OpenRobotics-official/Eurobot-competition/Electronics/Carte Coupe de France/Carte temp/Carte Stepper.PNG

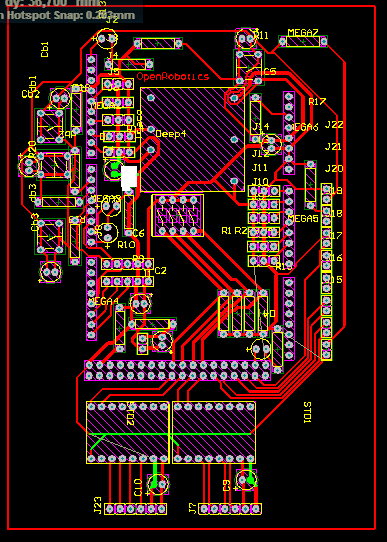
Electronics/Carte Coupe de France/Carte temp/Carte Stepper.PNG
