OpenRobotics-official/Eurobot-competition/Electronics/Carte Coupe de France/Carte temp/schematic carte stepper part1.PNG

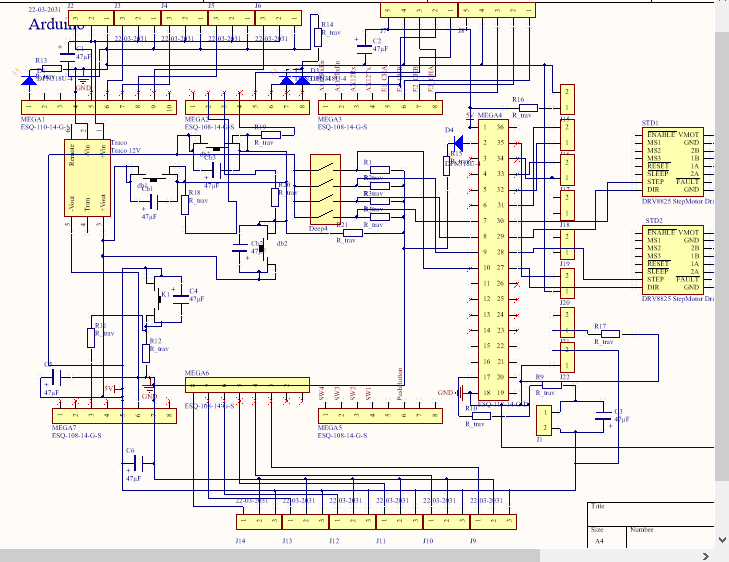
Electronics/Carte Coupe de France/Carte temp/schematic carte stepper part1.PNG
