OpenRobotics-official/Eurobot-competition/Electronics/Carte Coupe de France/Carte temp/schematic carte stepper part2.PNG

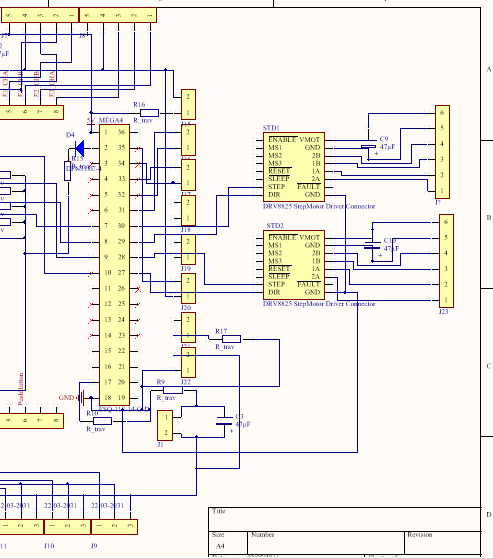
Electronics/Carte Coupe de France/Carte temp/schematic carte stepper part2.PNG
