OpenRobotics-official/Eurobot-competition/Electronics/Microcontrôleur/Screenshot_2015-12-03-18-33-24.png

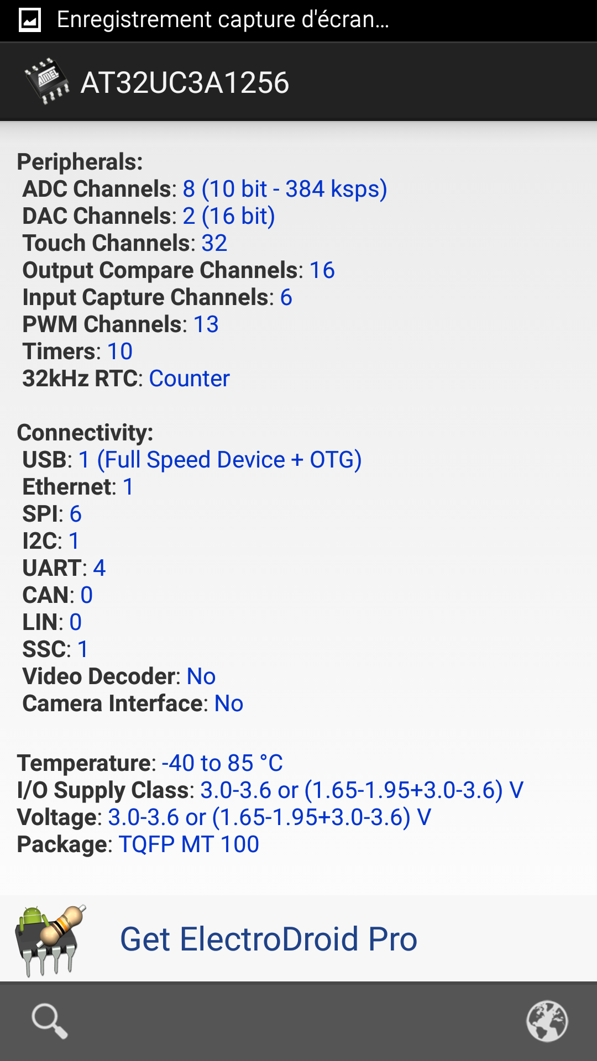
Electronics/Microcontrôleur/Screenshot_2015-12-03-18-33-24.png
