OpenRobotics-official/Eurobot-competition/wheelbase/Photo/wheelbase_trans.PNG

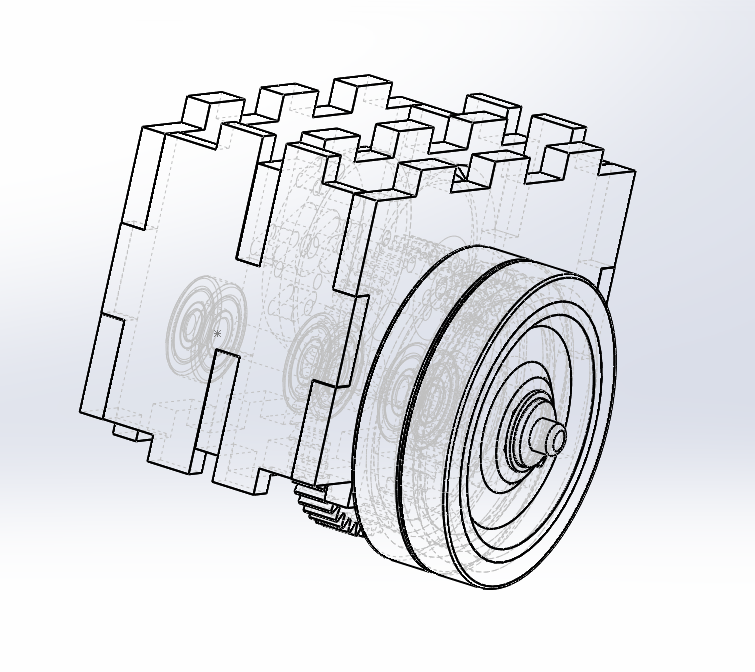
wheelbase/Photo/wheelbase_trans.PNG
