OpenRobotics-official/Eurobot-competition/wheelbase/solidworks/Base roulante lucas/base-roulante.PNG

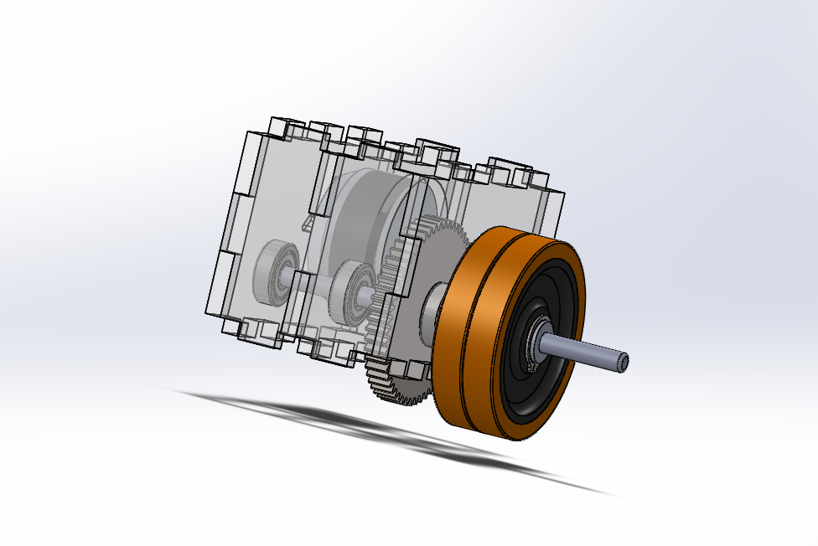
wheelbase/solidworks/Base roulante lucas/base-roulante.PNG
