OpenRobotics-official/Eurobot-competition/wheelbase/solidworks/Base roulante lucas/Banebots_double_T40.SLDASM

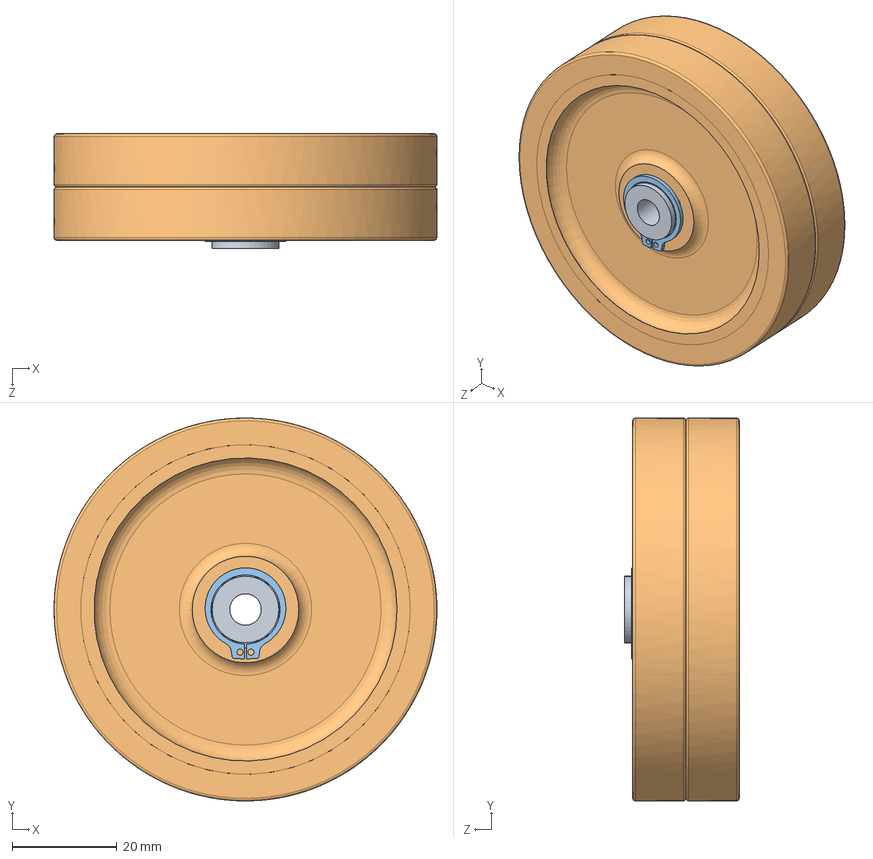
[picture p30: CAD file, 2016-05-19]
wheelbase/solidworks/Base roulante lucas/Banebots_double_T40.SLDASM
73.0 x 73.0 x 21.8 mm
T40H-SM62
BaneBots_T40 x 2
basic external retaining ring_ai
