OpenRobotics-official/Eurobot-competition/wheelbase/solidworks/Banebots_double_T40.SLDASM

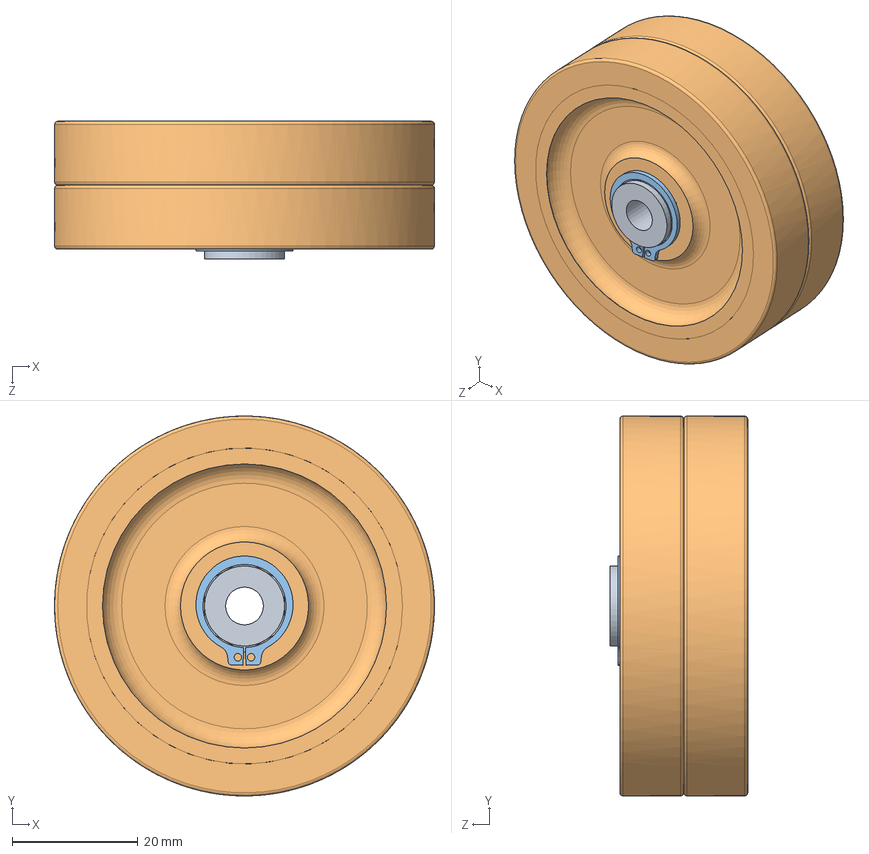
[picture p31: CAD file, 2016-05-19]
wheelbase/solidworks/Banebots_double_T40.SLDASM
60.3 x 60.3 x 21.8 mm
T40H-SM62
BaneBots_T40 x 2
basic external retaining ring_ai
