OpenRobotics-official/Eurobot-competition/3D-others/Support_axe_encondeurs.SLDPRT

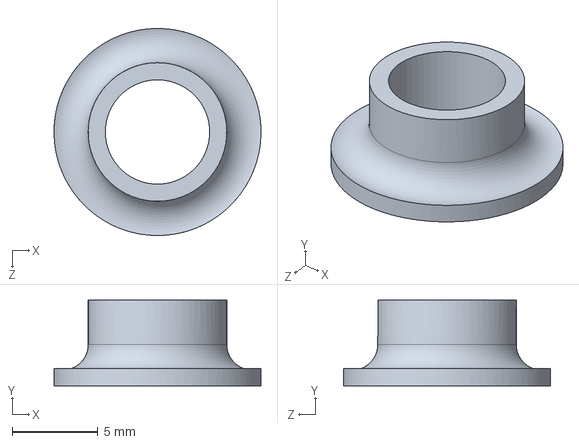
[picture p32: CAD file, 2016-05-19]
3D-others/Support_axe_encondeurs.SLDPRT
12.1 x 5.00 x 12.1 mm
