OpenRobotics-official/Eurobot-competition/Fishing arm/Support_bras_bloc.SLDPRT

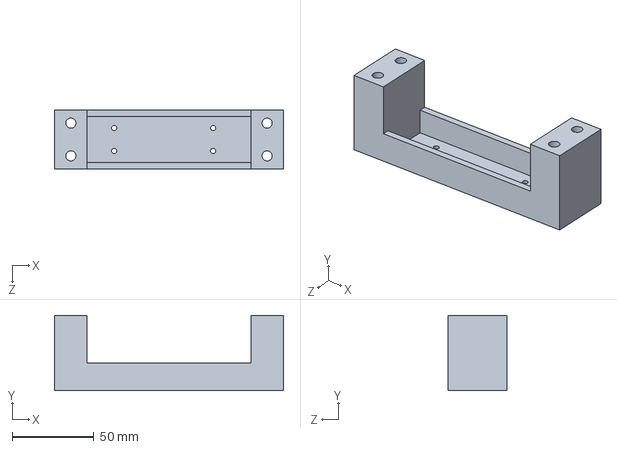
[picture p33: CAD file, 2016-05-19]
Fishing arm/Support_bras_bloc.SLDPRT
140.0 x 46.0 x 36.0 mm
