OpenRobotics-official/Eurobot-competition/Funny action/Parasol_v2/Servo.SLDPRT

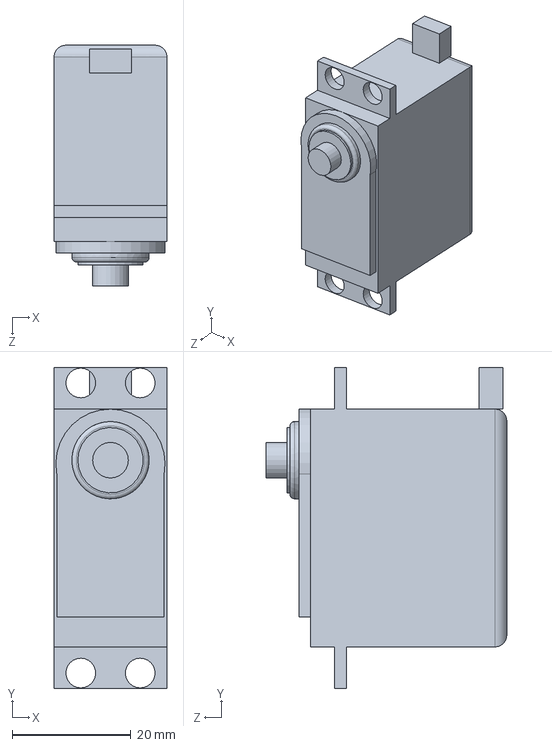
[picture p34: CAD file, 2016-05-19]
Funny action/Parasol_v2/Servo.SLDPRT
19.0 x 54.0 x 40.5 mm
