OpenRobotics-official/Eurobot-competition/wheelbase/base_dessous_V2_.DXF

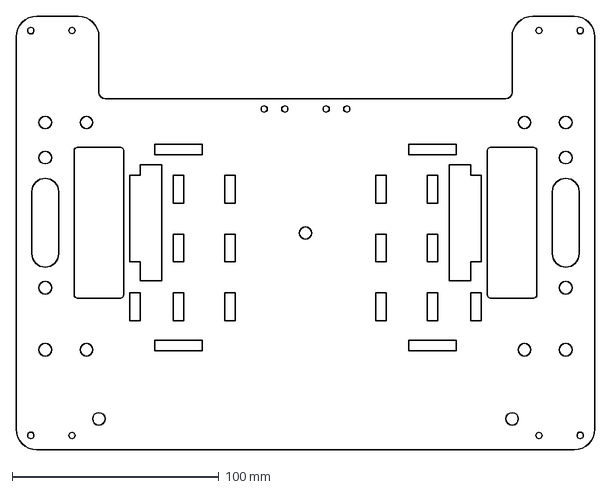
[picture p35: CAD file, 2016-05-19]
wheelbase/base_dessous_V2_.DXF
280.0 x 210.0 mm
