OpenRobotics-official/Eurobot-competition/wheelbase/Decoupe Laser/cote_long_roue.DXF

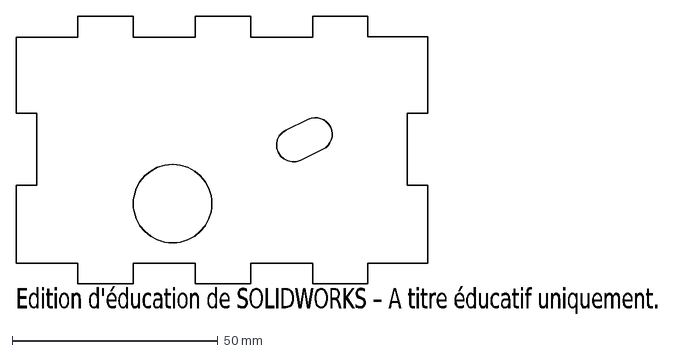
[picture p36: CAD file, 2016-05-19]
wheelbase/Decoupe Laser/cote_long_roue.DXF
Edition d'éducation de SOLIDWORKS – A titre éducatif uniquement.
