OpenRobotics-official/Eurobot-competition/wheelbase/Pieces a decouper/cote-court_50.DXF

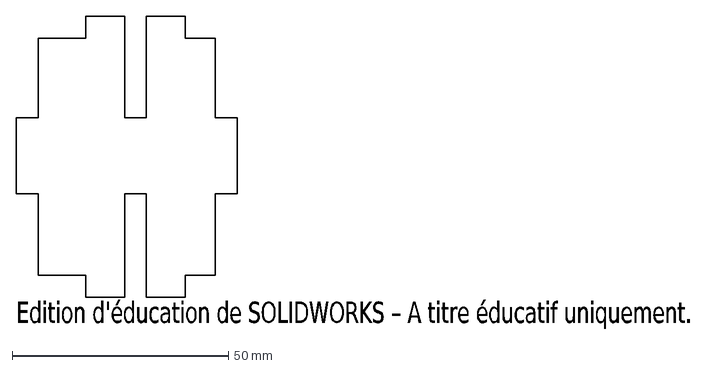
[picture p37: CAD file, 2016-05-19]
wheelbase/Pieces a decouper/cote-court_50.DXF
Edition d'éducation de SOLIDWORKS – A titre éducatif uniquement.
