OpenRobotics-official/Eurobot-competition/wheelbase/solidworks/Base roulante lucas/T40H-SM62.SLDPRT

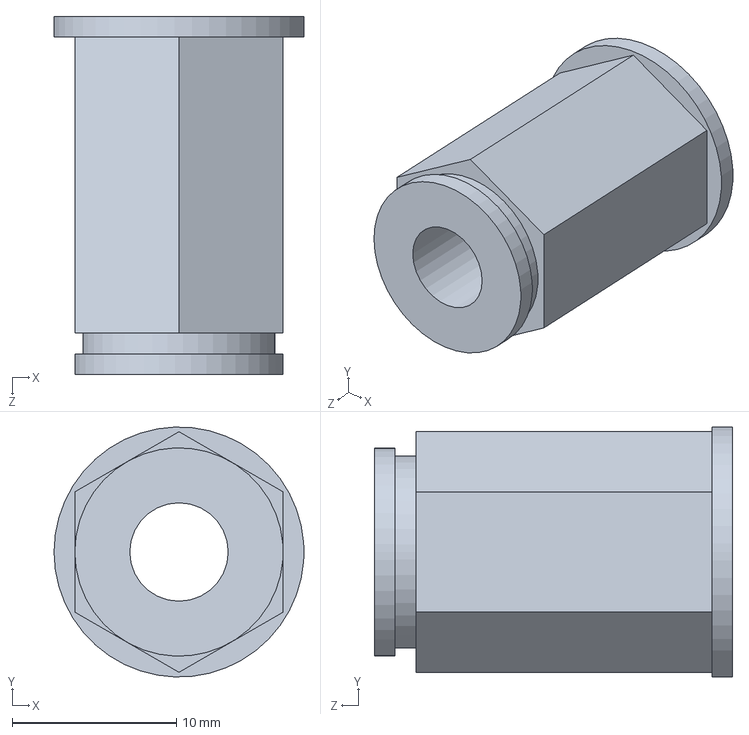
[picture p38: CAD file, 2016-05-19]
wheelbase/solidworks/Base roulante lucas/T40H-SM62.SLDPRT
15.2 x 15.2 x 21.8 mm
