OpenRobotics-official/Eurobot-competition/wheelbase/solidworks/STL/base_finale_style.STL

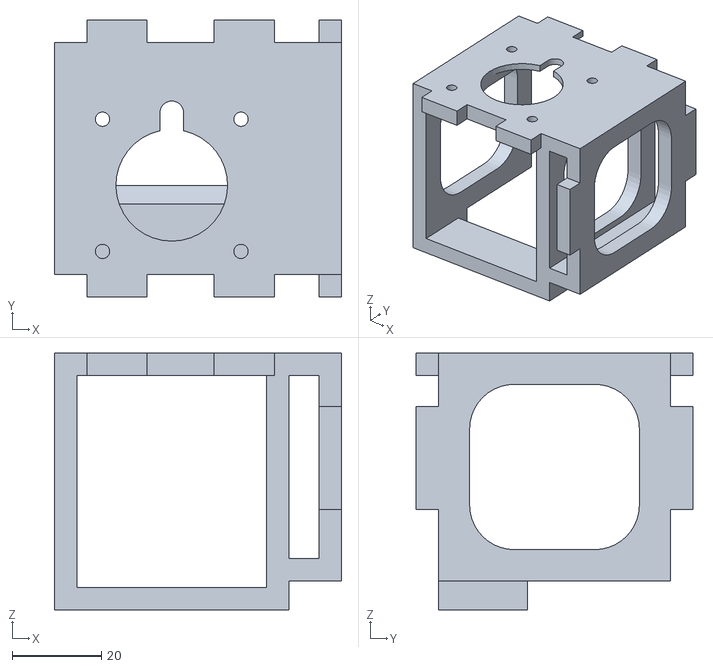
[picture p39: CAD file, 2016-05-19]
wheelbase/solidworks/STL/base_finale_style.STL
64.2 x 62.0 x 57.5
