OpenRobotics-official/Eurobot-competition/wheelbase/solidworks/U_jante_roue_POSIC_v4.SLDPRT

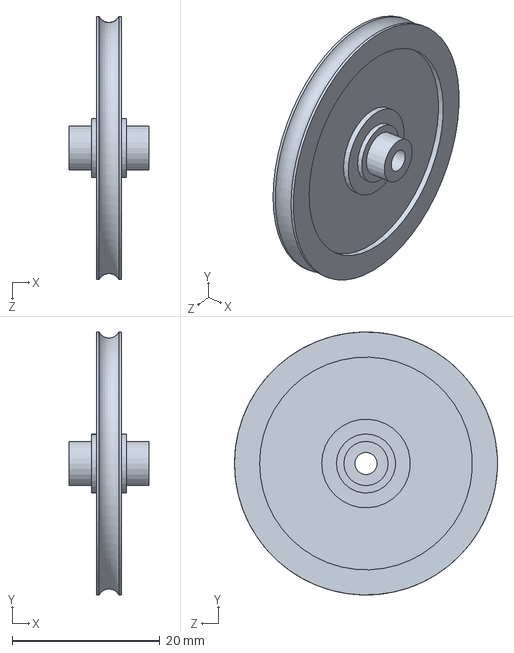
[picture p40: CAD file, 2016-05-19]
wheelbase/solidworks/U_jante_roue_POSIC_v4.SLDPRT
10.8 x 35.6 x 35.6 mm
