OpenRobotics-official/Eurobot-competition/3D-others/Support_trepied.SLDPRT

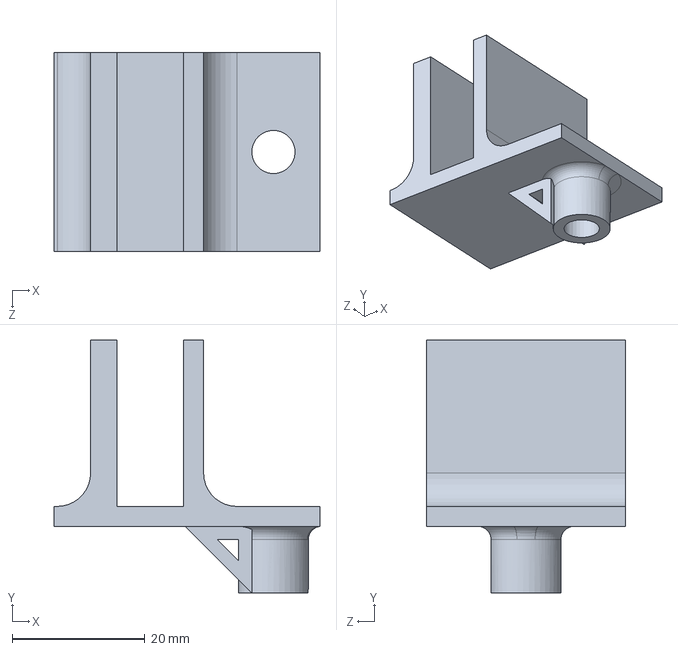
[picture p41: CAD file, 2016-05-19]
3D-others/Support_trepied.SLDPRT
40.0 x 38.0 x 30.0 mm
