OpenRobotics-official/Eurobot-competition/wheelbase/Decoupe Laser/cote-court_50.DXF

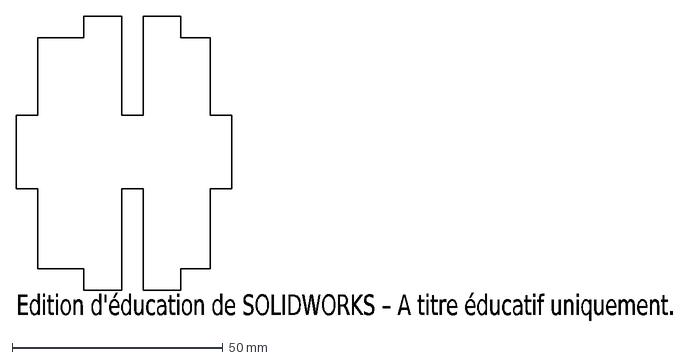
[picture p42: CAD file, 2016-05-19]
wheelbase/Decoupe Laser/cote-court_50.DXF
Edition d'éducation de SOLIDWORKS – A titre éducatif uniquement.
