OpenRobotics-official/Eurobot-competition/wheelbase/Pieces a decouper/cote_support_moteur_fin.DXF

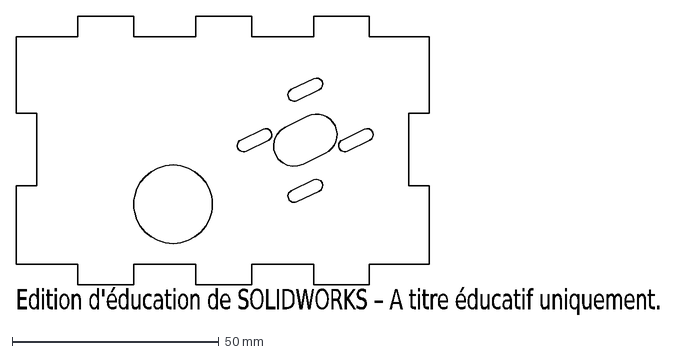
[picture p43: CAD file, 2016-05-19]
wheelbase/Pieces a decouper/cote_support_moteur_fin.DXF
Edition d'éducation de SOLIDWORKS – A titre éducatif uniquement.
