OpenRobotics-official/Eurobot-competition/wheelbase/solidworks/Base roulante lucas/cote_support_moteur_fin.SLDPRT

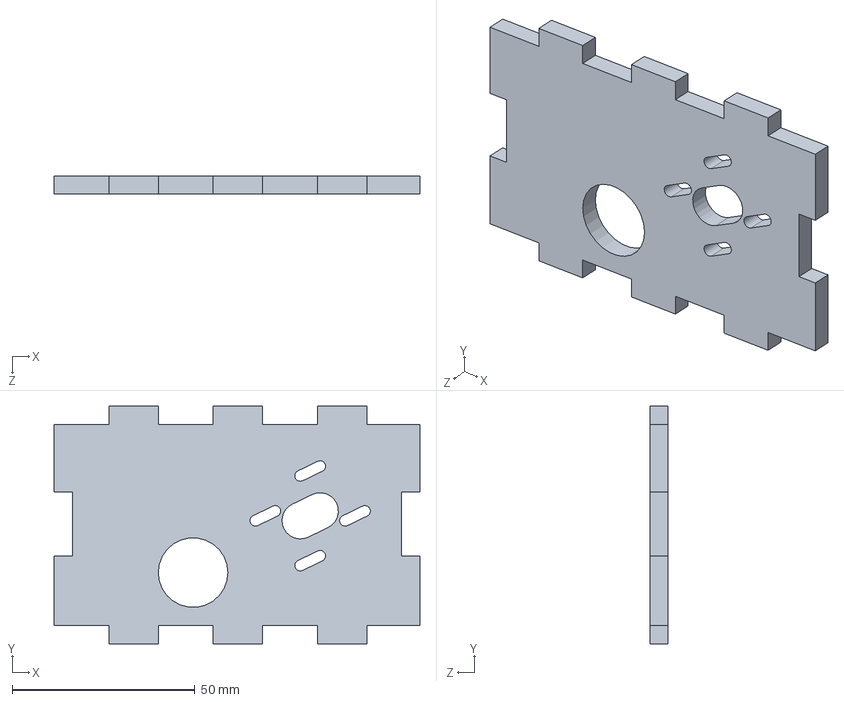
[picture p44: CAD file, 2016-05-19]
wheelbase/solidworks/Base roulante lucas/cote_support_moteur_fin.SLDPRT
100.0 x 65.0 x 5.00 mm
