OpenRobotics-official/Eurobot-competition/wheelbase/solidworks/coding_wheel.SLDPRT

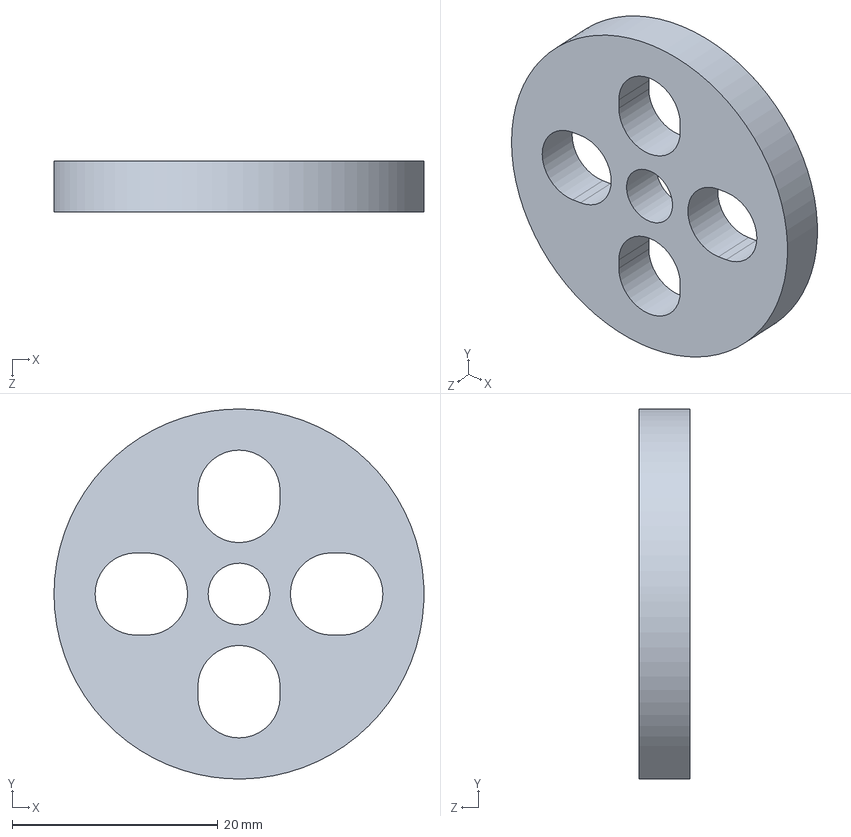
[picture p45: CAD file, 2016-05-19]
wheelbase/solidworks/coding_wheel.SLDPRT
36.0 x 36.0 x 5.00 mm
