OpenRobotics-official/Eurobot-competition/3D-others/Support Tirette.SLDPRT

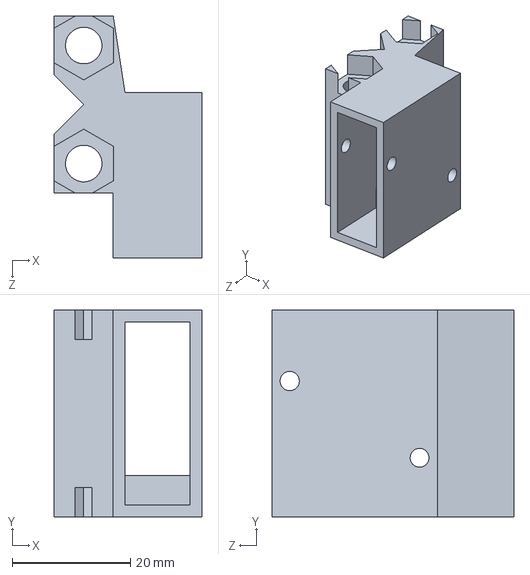
[picture p46: CAD file, 2016-05-19]
3D-others/Support Tirette.SLDPRT
25.0 x 35.0 x 41.0 mm
