OpenRobotics-official/Eurobot-competition/Fishing arm/support_servo_v3.SLDPRT

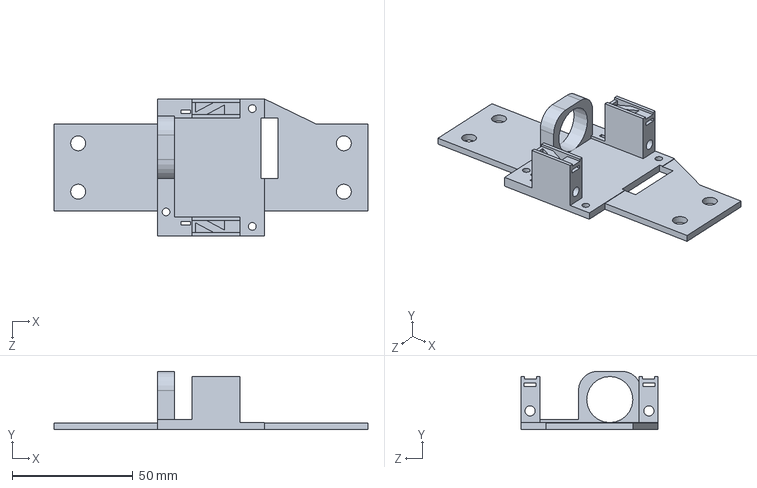
[picture p47: CAD file, 2016-05-19]
Fishing arm/support_servo_v3.SLDPRT
130.0 x 24.2 x 56.8 mm
