OpenRobotics-official/Eurobot-competition/Funny action/Parasol_v2/Bar_tissu_robot.SLDPRT

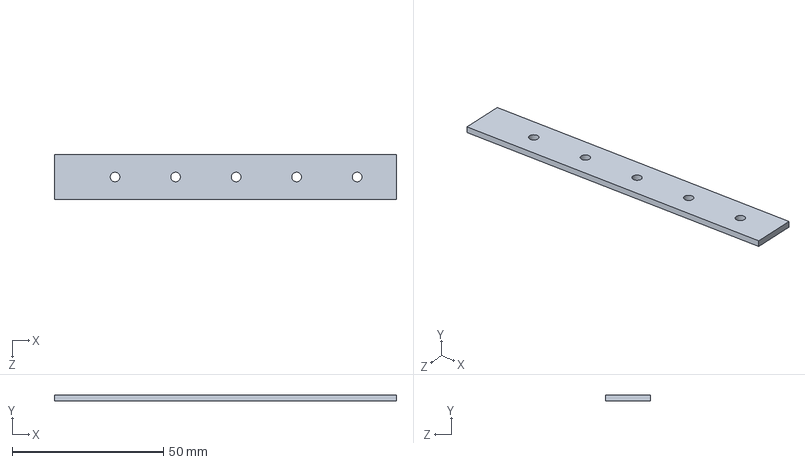
[picture p48: CAD file, 2016-05-19]
Funny action/Parasol_v2/Bar_tissu_robot.SLDPRT
113.0 x 2.00 x 15.0 mm
