OpenRobotics-official/Eurobot-competition/wheelbase/Decoupe Laser/cote_long_milieu.DXF

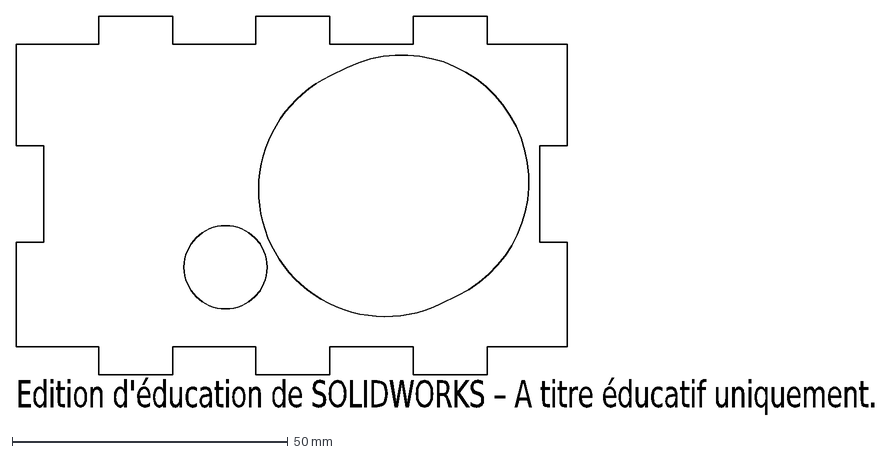
[picture p49: CAD file, 2016-05-19]
wheelbase/Decoupe Laser/cote_long_milieu.DXF
Edition d'éducation de SOLIDWORKS – A titre éducatif uniquement.
