OpenRobotics-official/Eurobot-competition/wheelbase/Pieces a decouper/cote_long_roue.DXF

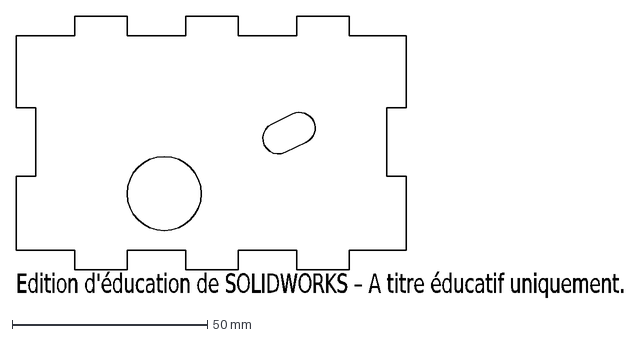
[picture p50: CAD file, 2016-05-19]
wheelbase/Pieces a decouper/cote_long_roue.DXF
Edition d'éducation de SOLIDWORKS – A titre éducatif uniquement.
