OpenRobotics-official/Eurobot-competition/wheelbase/solidworks/Base roulante lucas/cote-court_50.SLDPRT

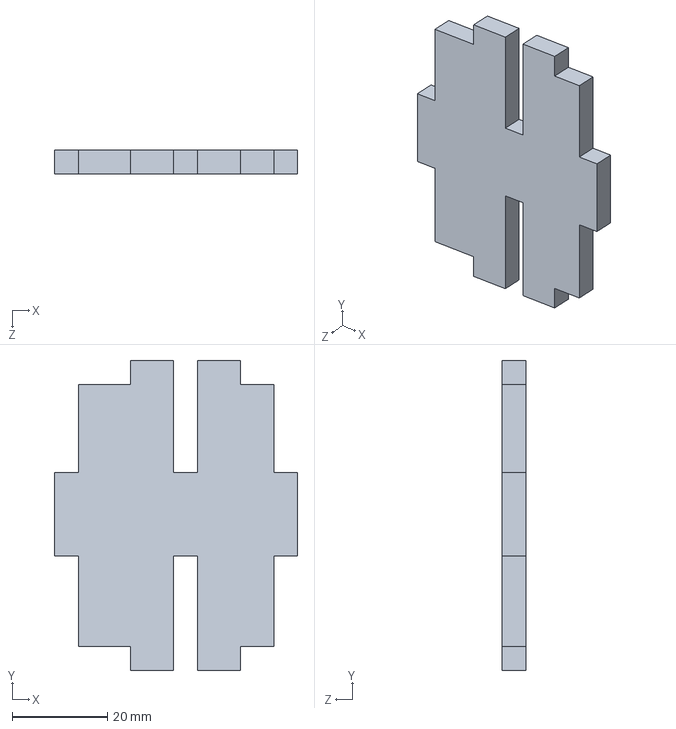
[picture p51: CAD file, 2016-05-19]
wheelbase/solidworks/Base roulante lucas/cote-court_50.SLDPRT
51.0 x 65.0 x 5.00 mm
