OpenRobotics-official/Eurobot-competition/3D-others/Support_bille_folle.SLDPRT

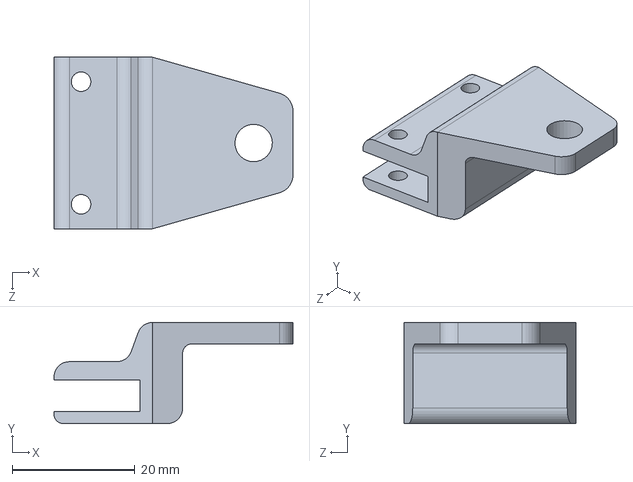
[picture p52: CAD file, 2016-05-19]
3D-others/Support_bille_folle.SLDPRT
39.0 x 16.5 x 28.0 mm
