OpenRobotics-official/Eurobot-competition/Funny action/Parasol_v2/Bar_U.SLDPRT

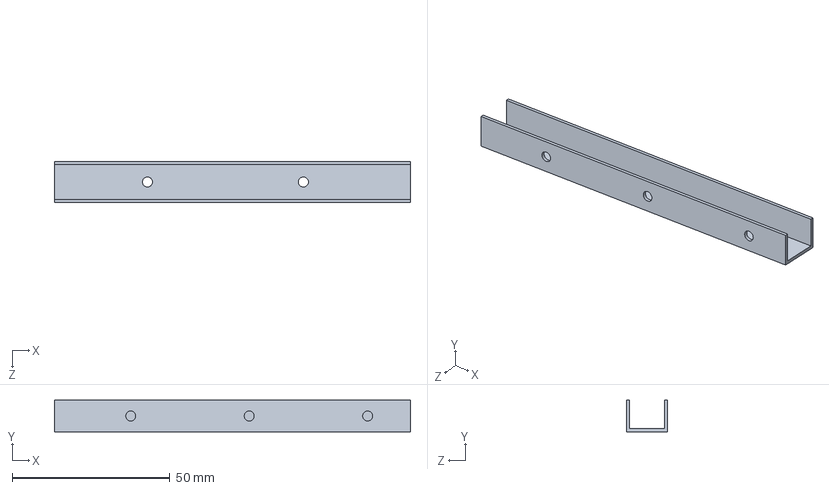
[picture p53: CAD file, 2016-05-19]
Funny action/Parasol_v2/Bar_U.SLDPRT
113.0 x 10.0 x 13.0 mm
