OpenRobotics-official/Eurobot-competition/wheelbase/Decoupe Laser/cote_support_moteur_fin.DXF

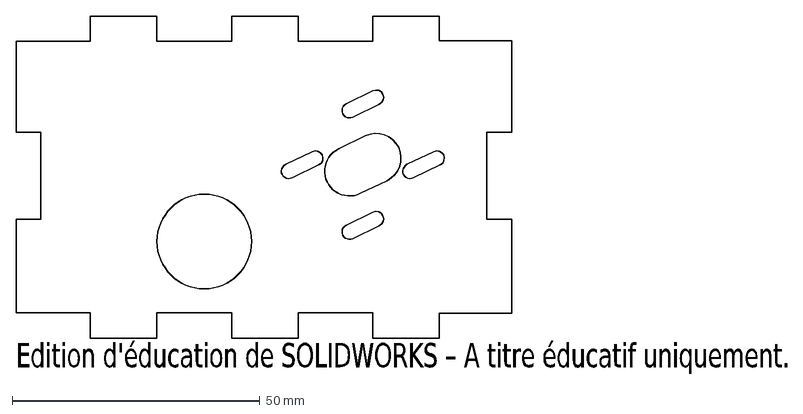
[picture p54: CAD file, 2016-05-19]
wheelbase/Decoupe Laser/cote_support_moteur_fin.DXF
Edition d'éducation de SOLIDWORKS – A titre éducatif uniquement.
