OpenRobotics-official/Eurobot-competition/wheelbase/Pieces a decouper/cote_long_milieu.DXF

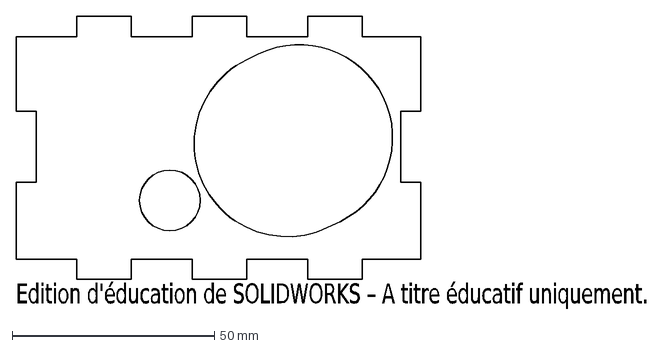
[picture p55: CAD file, 2016-05-19]
wheelbase/Pieces a decouper/cote_long_milieu.DXF
Edition d'éducation de SOLIDWORKS – A titre éducatif uniquement.
