OpenRobotics-official/Eurobot-competition/wheelbase/solidworks/Base roulante lucas/base_dessus.SLDPRT

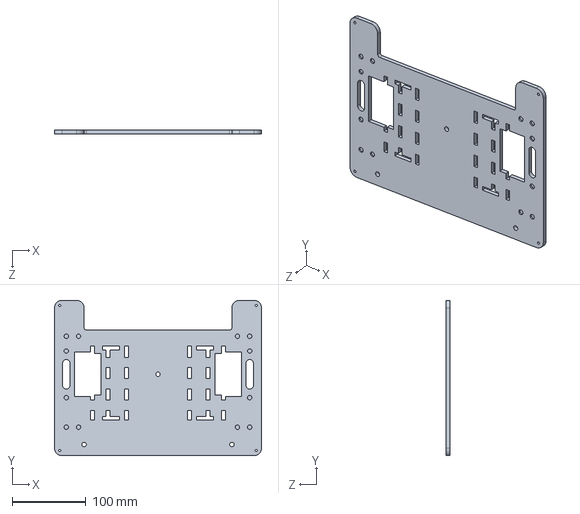
[picture p56: CAD file, 2016-05-19]
wheelbase/solidworks/Base roulante lucas/base_dessus.SLDPRT
280.0 x 210.0 x 5.00 mm
