OpenRobotics-official/Eurobot-competition/wheelbase/solidworks/Quanum360 Cage.SLDPRT

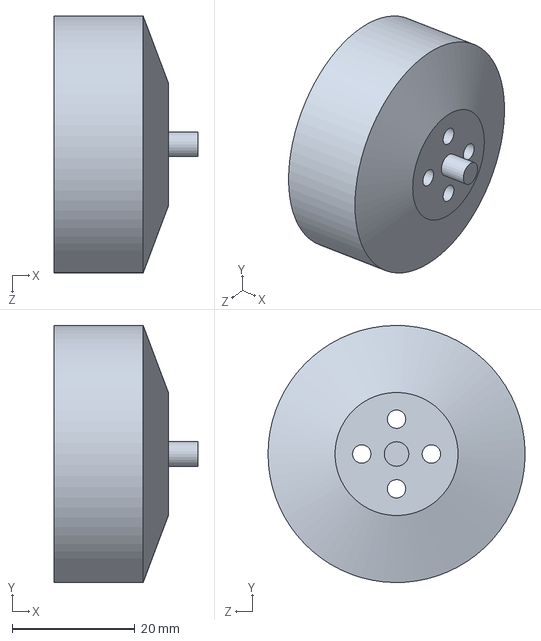
[picture p57: CAD file, 2016-05-19]
wheelbase/solidworks/Quanum360 Cage.SLDPRT
23.4 x 41.8 x 41.8 mm
