OpenRobotics-official/Eurobot-competition/3D-others/support_plaque_sponsor.SLDPRT

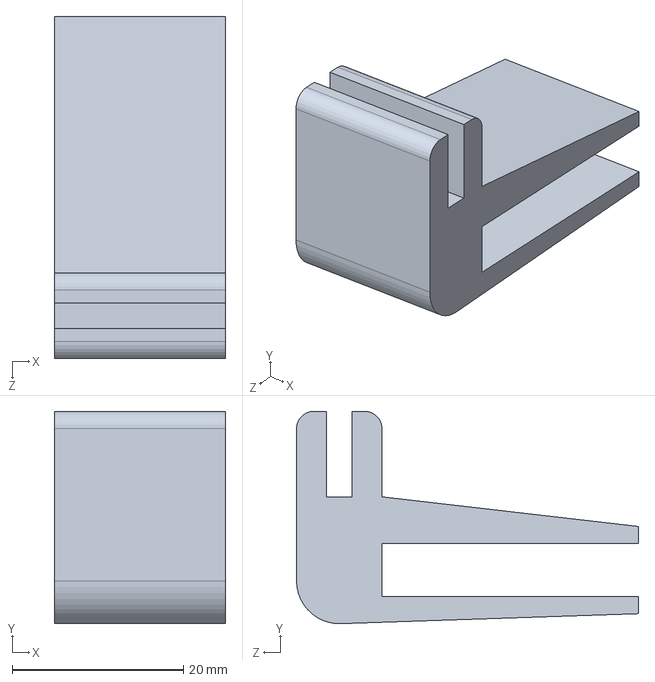
[picture p58: CAD file, 2016-05-19]
3D-others/support_plaque_sponsor.SLDPRT
20.0 x 24.8 x 40.0 mm
