OpenRobotics-official/Eurobot-competition/Fishing arm/Plaque_support_poisson.SLDPRT

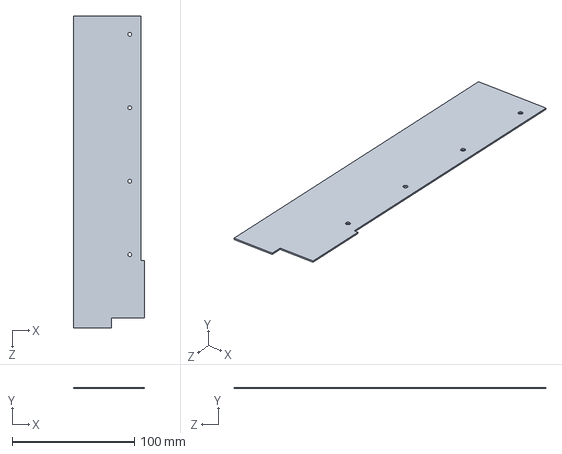
[picture p59: CAD file, 2016-05-19]
Fishing arm/Plaque_support_poisson.SLDPRT
58.0 x 1.00 x 255.0 mm
