OpenRobotics-official/Eurobot-competition/Funny action/Parasol_v2/Bar_angle.SLDPRT

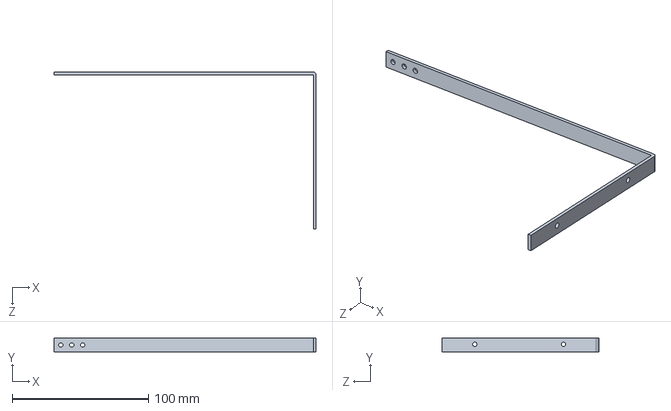
[picture p60: CAD file, 2016-05-19]
Funny action/Parasol_v2/Bar_angle.SLDPRT
192.0 x 10.0 x 115.0 mm
