OpenRobotics-official/Eurobot-competition/wheelbase/Pieces a decouper/coding_wheel.DXF

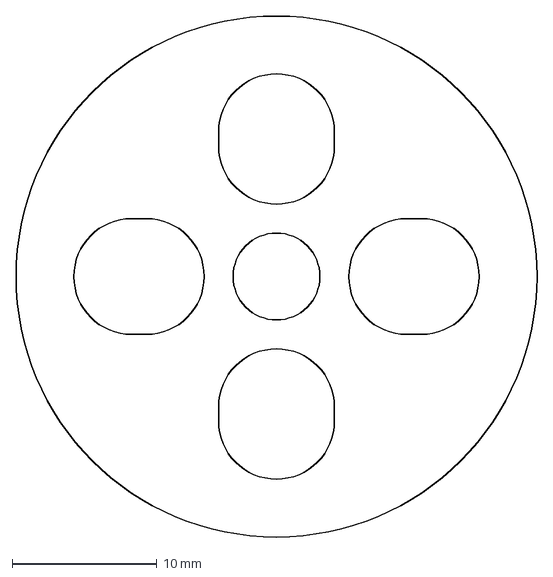
[picture p61: CAD file, 2016-05-19]
wheelbase/Pieces a decouper/coding_wheel.DXF
36.0 x 36.0 mm
