OpenRobotics-official/Eurobot-competition/wheelbase/solidworks/Base roulante lucas/BaneBots_T40.SLDPRT

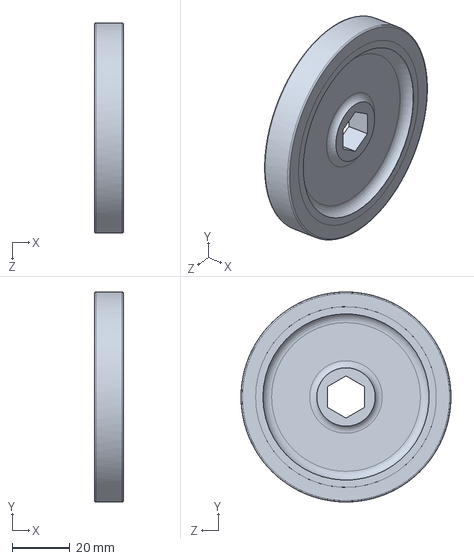
[picture p62: CAD file, 2016-05-19]
wheelbase/solidworks/Base roulante lucas/BaneBots_T40.SLDPRT
10.2 x 73.0 x 73.0 mm
