OpenRobotics-official/Eurobot-competition/wheelbase/solidworks/STL/base_stepper_symFAIT_1.SLDPRT

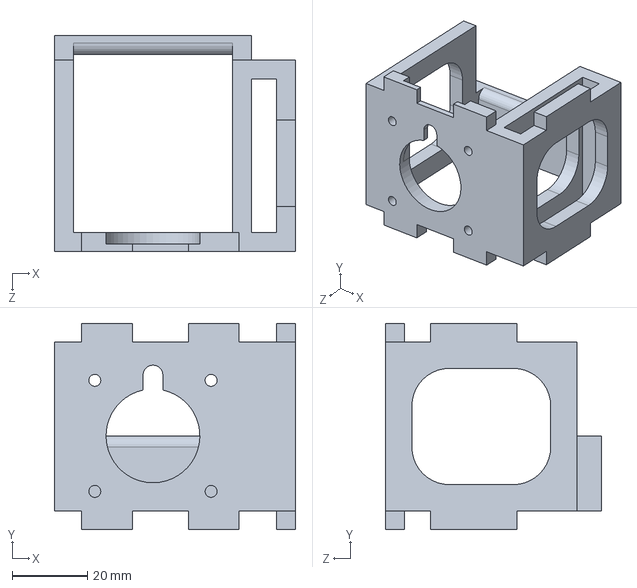
[picture p63: CAD file, 2016-05-19]
wheelbase/solidworks/STL/base_stepper_symFAIT_1.SLDPRT
64.2 x 55.0 x 57.5 mm
