OpenRobotics-official/Eurobot-competition/3D-others/tirette.SLDPRT

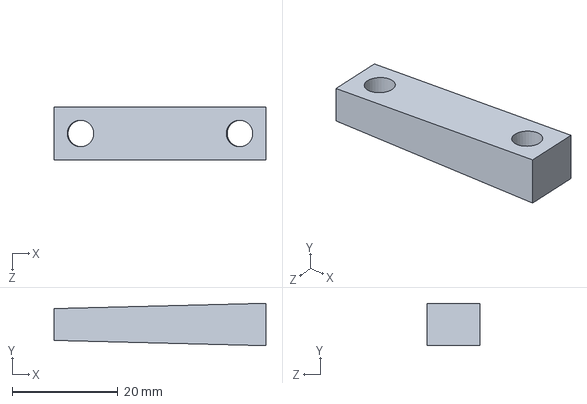
[picture p64: CAD file, 2016-05-19]
3D-others/tirette.SLDPRT
40.0 x 8.00 x 10.0 mm
