OpenRobotics-official/Eurobot-competition/Fishing arm/Accessoire_servo_rondelle.SLDPRT

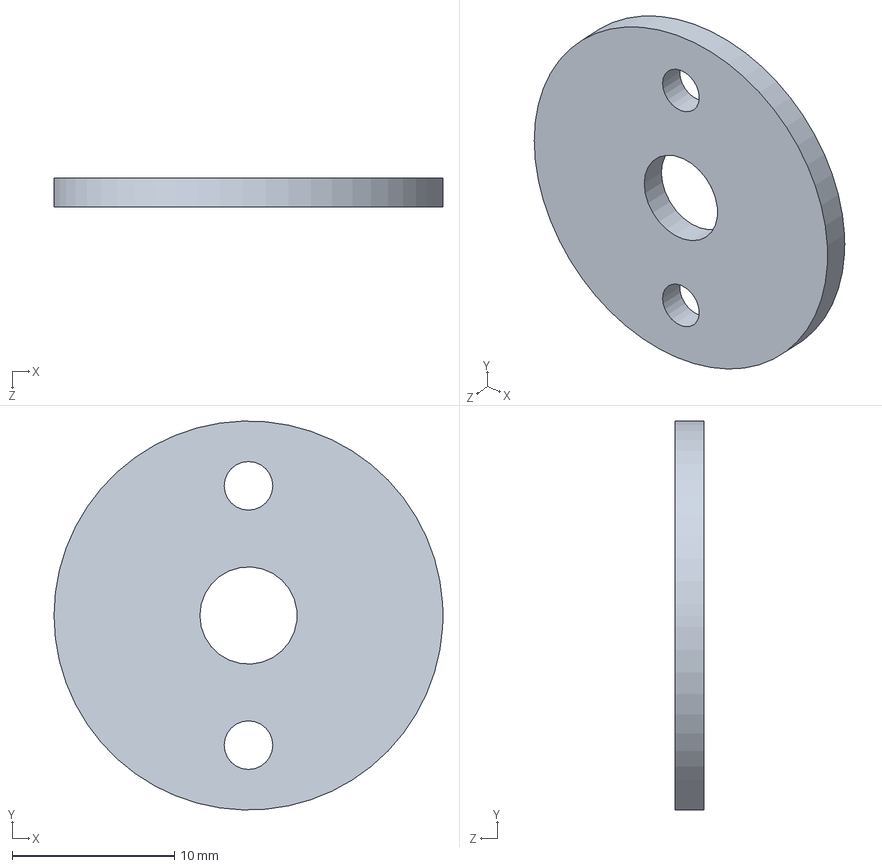
[picture p65: CAD file, 2016-05-19]
Fishing arm/Accessoire_servo_rondelle.SLDPRT
24.0 x 24.0 x 1.80 mm
