OpenRobotics-official/Eurobot-competition/wheelbase/solidworks/Base roulante lucas/Spur gear 54.SLDPRT

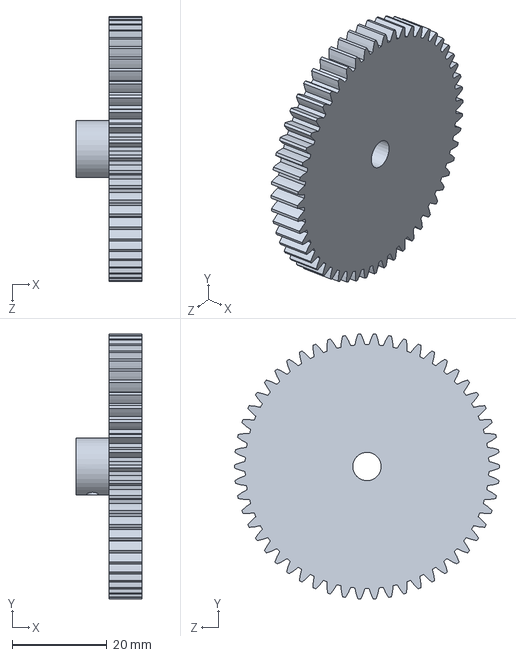
[picture p66: CAD file, 2016-05-19]
wheelbase/solidworks/Base roulante lucas/Spur gear 54.SLDPRT
14.0 x 55.9 x 56.0 mm
