OpenRobotics-official/Eurobot-competition/wheelbase/solidworks/Quanum360 base.SLDPRT

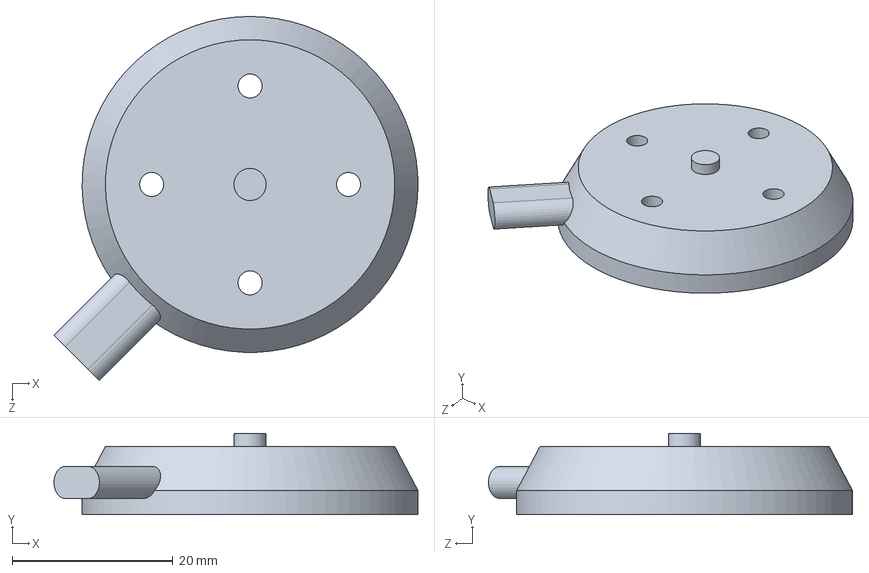
[picture p67: CAD file, 2016-05-19]
wheelbase/solidworks/Quanum360 base.SLDPRT
45.3 x 10.1 x 45.3 mm
