OpenRobotics-official/Eurobot-competition/wheelbase/solidworks/STL/Adaptateur_roues.STL

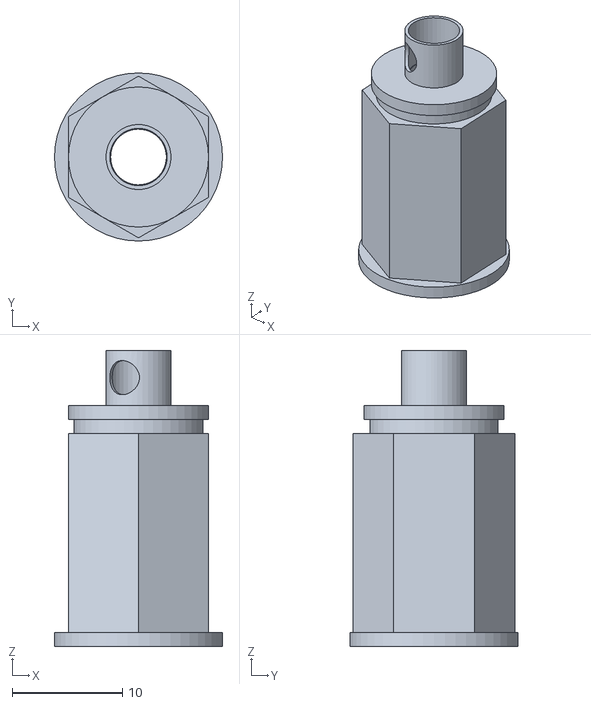
[picture p68: CAD file, 2016-05-19]
wheelbase/solidworks/STL/Adaptateur_roues.STL
15.2 x 15.2 x 26.8
