OpenRobotics-official/Eurobot-competition/Funny action/Parasol_v2/Bar_u_robot.SLDPRT

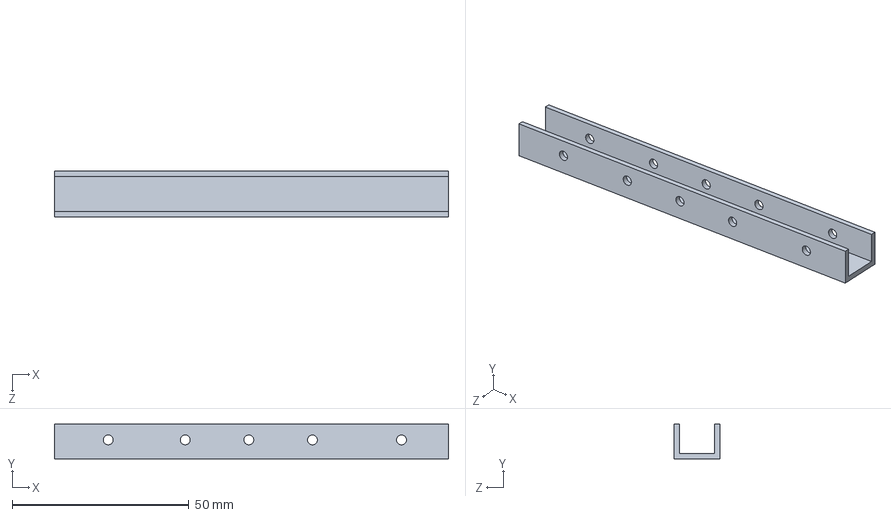
[picture p69: CAD file, 2016-05-19]
Funny action/Parasol_v2/Bar_u_robot.SLDPRT
111.5 x 9.90 x 13.0 mm
