OpenRobotics-official/Eurobot-competition/Fishing arm/Petite_piece_Lego.SLDPRT

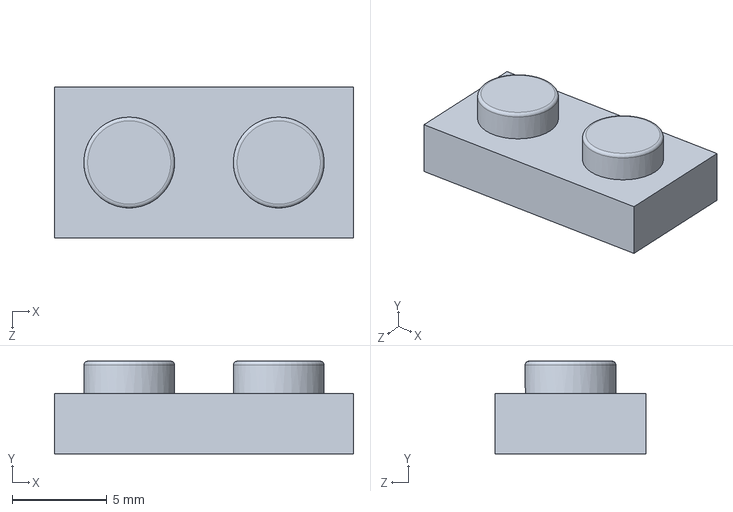
[picture p70: CAD file, 2016-05-19]
Fishing arm/Petite_piece_Lego.SLDPRT
15.8 x 4.90 x 8.00 mm
