OpenRobotics-official/Eurobot-competition/wheelbase/solidworks/Base roulante lucas/inside ball bearing 6.6.19.SLDPRT

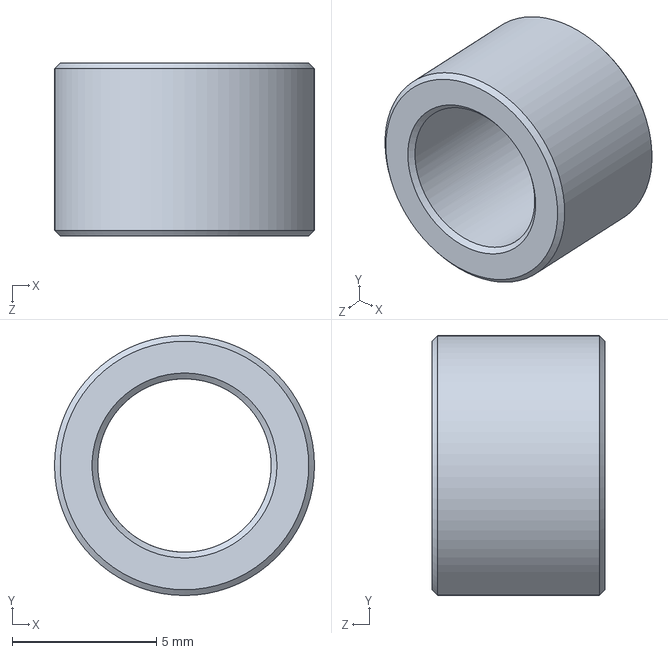
[picture p71: CAD file, 2016-05-19]
wheelbase/solidworks/Base roulante lucas/inside ball bearing 6.6.19.SLDPRT
9.00 x 9.00 x 6.00 mm
