OpenRobotics-official/Eurobot-competition/Fishing arm/Plaquette.SLDPRT

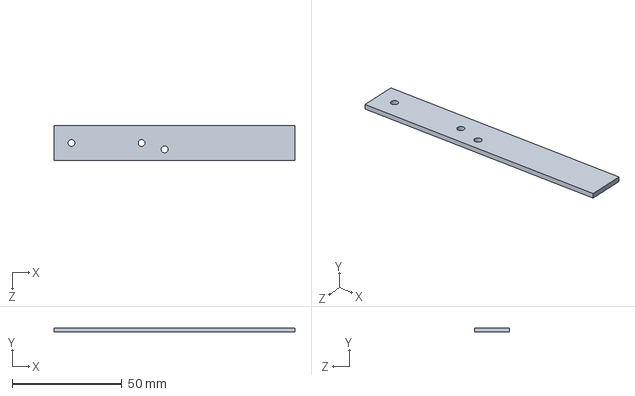
[picture p72: CAD file, 2016-05-19]
Fishing arm/Plaquette.SLDPRT
110.0 x 2.00 x 16.0 mm
