OpenRobotics-official/Eurobot-competition/wheelbase/solidworks/codeur_face2.SLDPRT

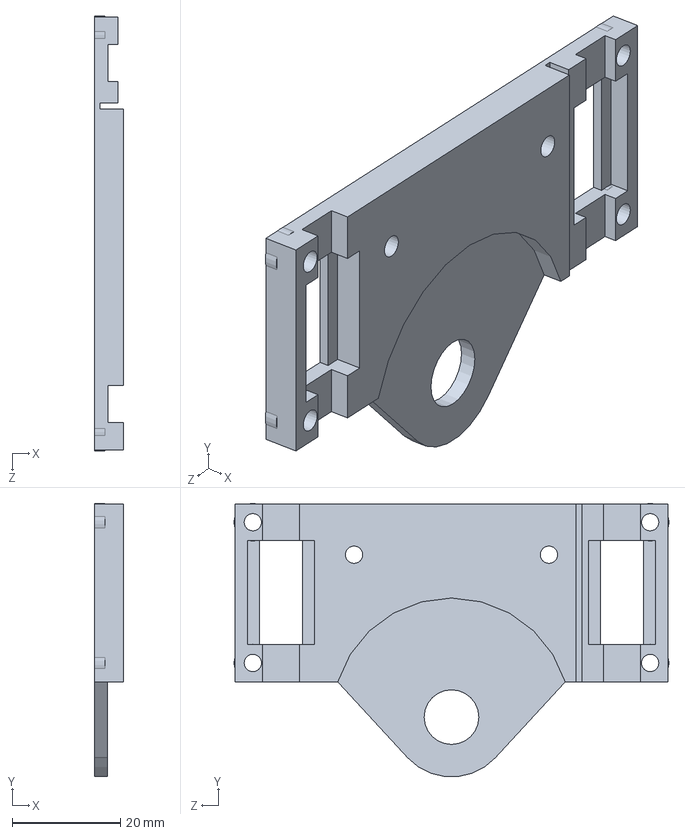
[picture p73: CAD file, 2016-05-19]
wheelbase/solidworks/codeur_face2.SLDPRT
5.40 x 50.4 x 80.3 mm
