OpenRobotics-official/Eurobot-competition/Fishing arm/Element_Charniere.SLDPRT

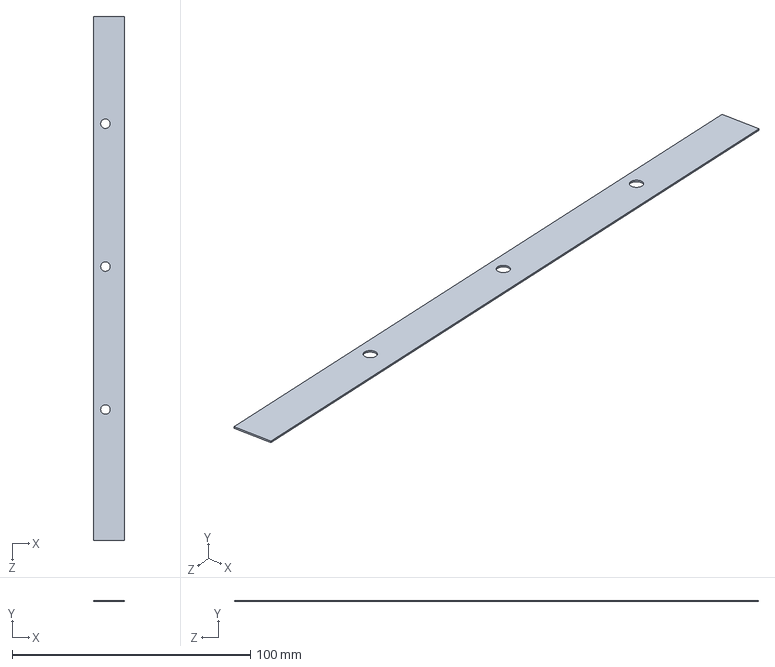
[picture p74: CAD file, 2016-05-19]
Fishing arm/Element_Charniere.SLDPRT
13.0 x 0.5 x 220.0 mm
