OpenRobotics-official/Eurobot-competition/wheelbase/solidworks/spur gear 12.SLDPRT

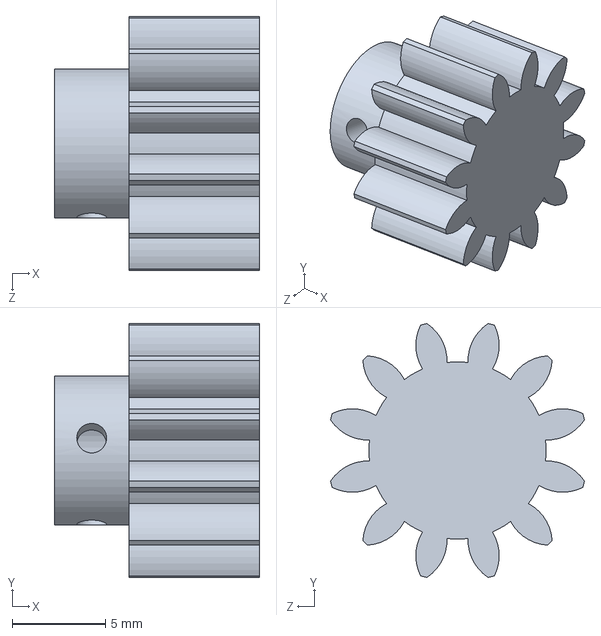
[picture p75: CAD file, 2016-05-19]
wheelbase/solidworks/spur gear 12.SLDPRT
11.0 x 13.6 x 13.6 mm
