OpenRobotics-official/Eurobot-competition/wheelbase/solidworks/STL/base_stepper_symTROU_fait.STL

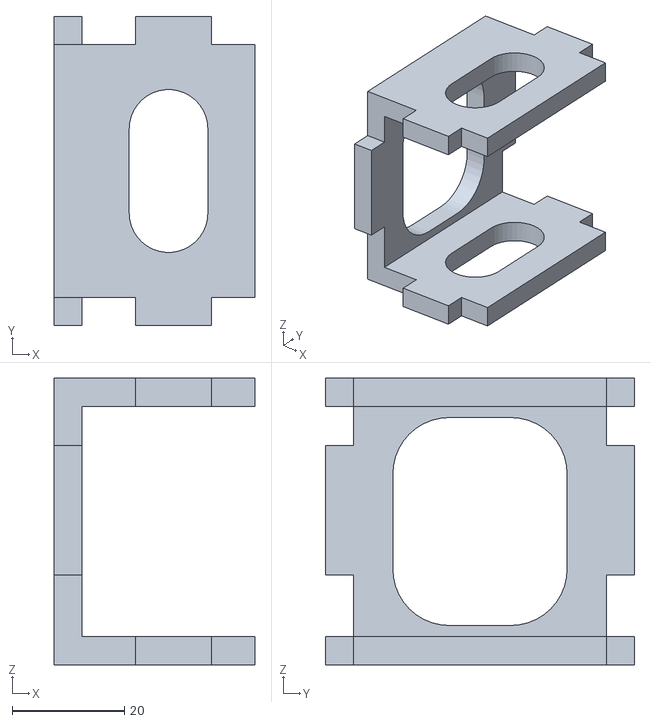
[picture p76: CAD file, 2016-05-19]
wheelbase/solidworks/STL/base_stepper_symTROU_fait.STL
35.8 x 55.0 x 51.0
