OpenRobotics-official/Eurobot-competition/Fishing arm/inside_link_bearing.SLDPRT

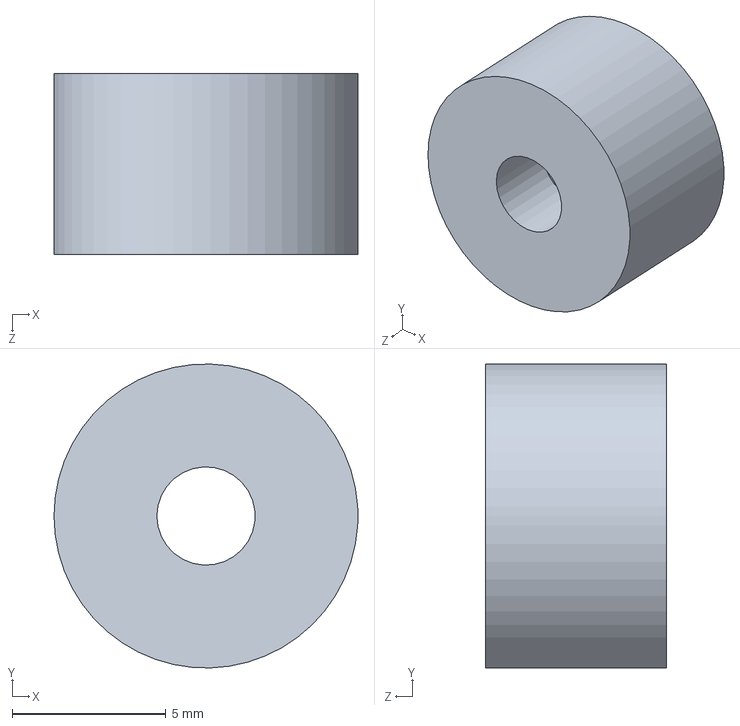
[picture p77: CAD file, 2016-05-19]
Fishing arm/inside_link_bearing.SLDPRT
9.90 x 9.90 x 5.90 mm
