OpenRobotics-official/Eurobot-competition/Fishing arm/Support_bras_support_cylindre.SLDPRT

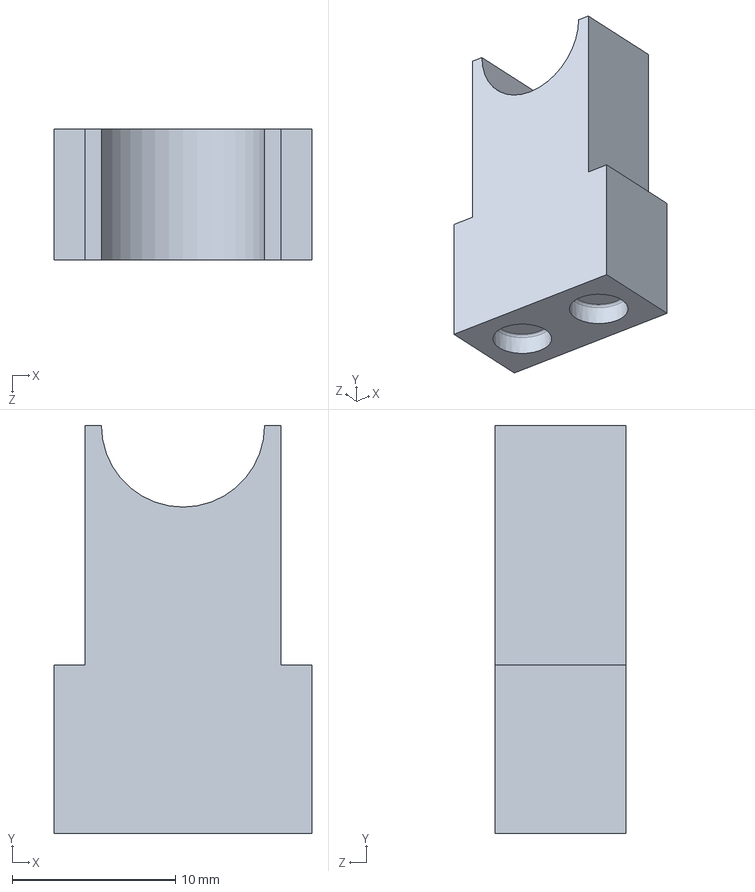
[picture p78: CAD file, 2016-05-19]
Fishing arm/Support_bras_support_cylindre.SLDPRT
15.8 x 25.0 x 8.00 mm
