OpenRobotics-official/Eurobot-competition/Fishing arm/Support_bras_roulement.SLDPRT

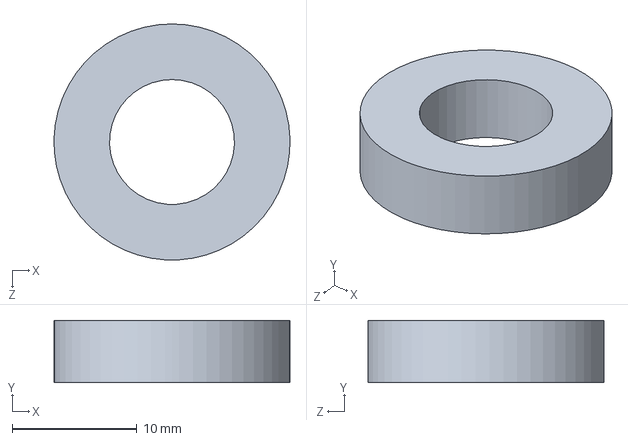
[picture p79: CAD file, 2016-05-19]
Fishing arm/Support_bras_roulement.SLDPRT
18.9 x 5.00 x 18.9 mm
