OpenRobotics-official/Eurobot-competition/wheelbase/solidworks/coding_wheel_2.SLDPRT

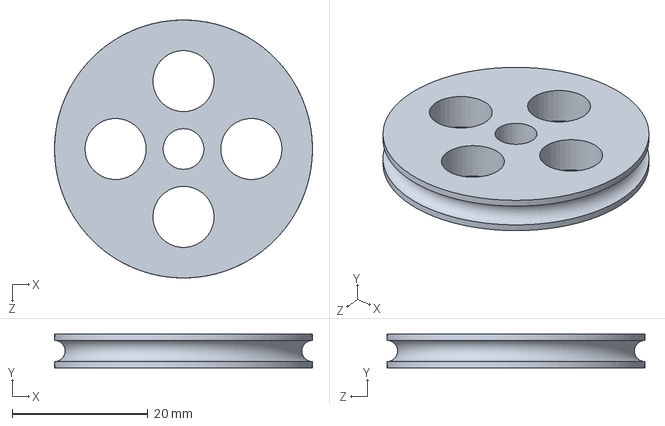
[picture p80: CAD file, 2016-05-19]
wheelbase/solidworks/coding_wheel_2.SLDPRT
38.0 x 5.00 x 38.0 mm
