OpenRobotics-official/Eurobot-competition/Fishing arm/Plaque_support_aimant.SLDPRT

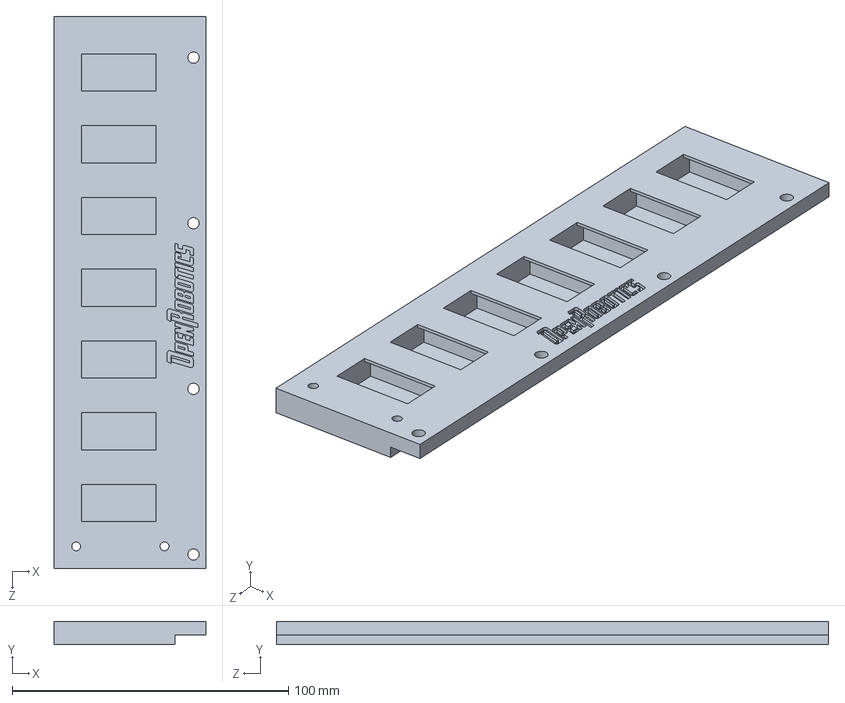
[picture p82: CAD file, 2016-05-19]
Fishing arm/Plaque_support_aimant.SLDPRT
55.0 x 8.50 x 200.0 mm
