OpenRobotics-official/Eurobot-competition/Fishing arm/Element_charniere_plastique.SLDPRT

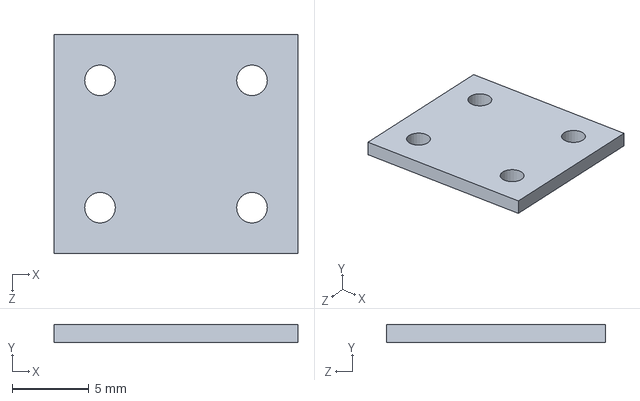
[picture p83: CAD file, 2016-05-19]
Fishing arm/Element_charniere_plastique.SLDPRT
15.9 x 1.20 x 14.3 mm
