OpenRobotics-official/Eurobot-competition/Fishing arm/Support_bras_base.SLDPRT

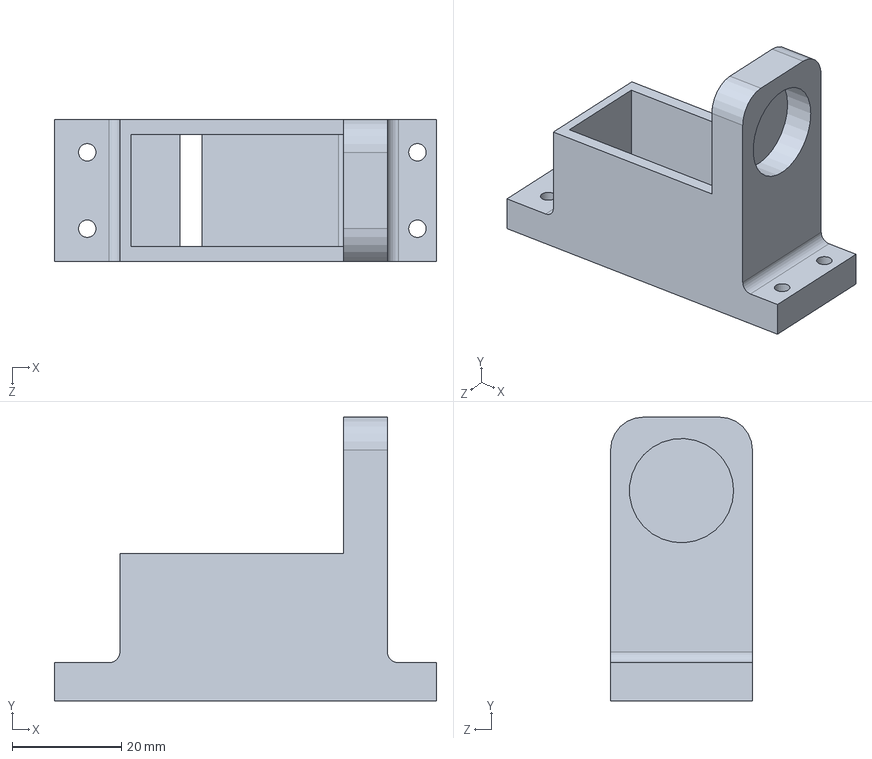
[picture p84: CAD file, 2016-05-19]
Fishing arm/Support_bras_base.SLDPRT
70.0 x 52.0 x 26.0 mm
