OpenRobotics-official/Eurobot-competition/wheelbase/solidworks/Base roulante lucas/cote_long_milieu.SLDPRT

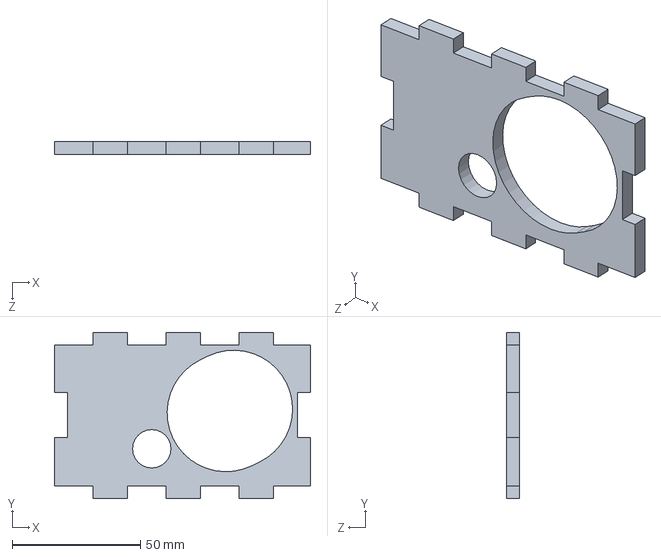
[picture p85: CAD file, 2016-05-19]
wheelbase/solidworks/Base roulante lucas/cote_long_milieu.SLDPRT
100.0 x 65.0 x 5.00 mm
