OpenRobotics-official/Eurobot-competition/Fishing arm/Support_bras_axe_rotatif.SLDPRT

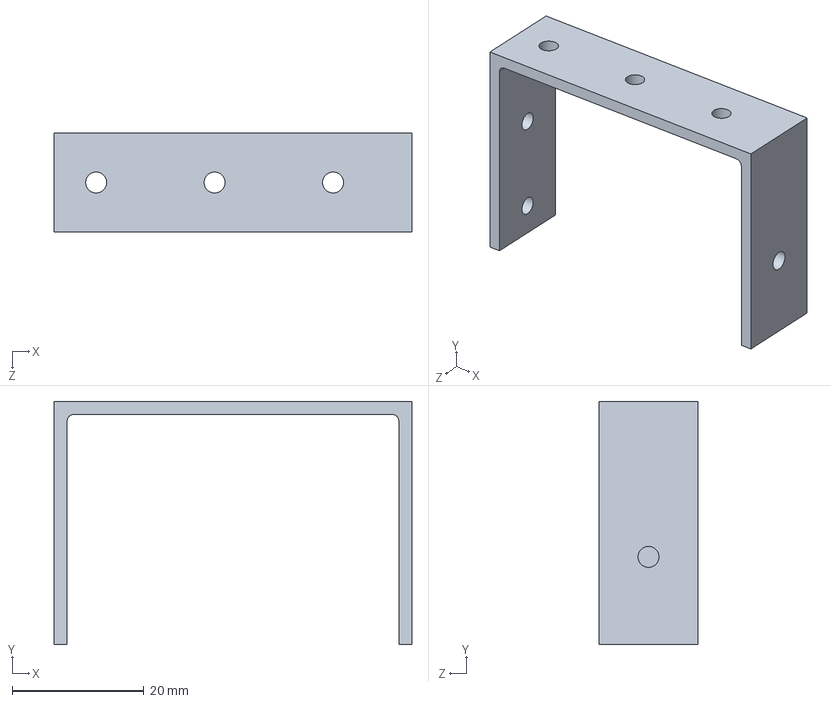
[picture p86: CAD file, 2016-05-19]
Fishing arm/Support_bras_axe_rotatif.SLDPRT
54.4 x 37.0 x 15.0 mm
