OpenRobotics-official/Eurobot-competition/wheelbase/solidworks/Base roulante lucas/tige-roue.SLDPRT

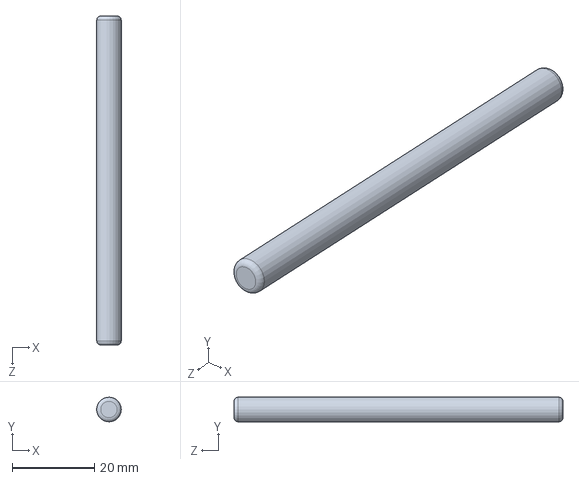
[picture p87: CAD file, 2016-05-19]
wheelbase/solidworks/Base roulante lucas/tige-roue.SLDPRT
5.98 x 5.99 x 80.0 mm
