OpenRobotics-official/Eurobot-competition/Fishing arm/support_servo.SLDPRT

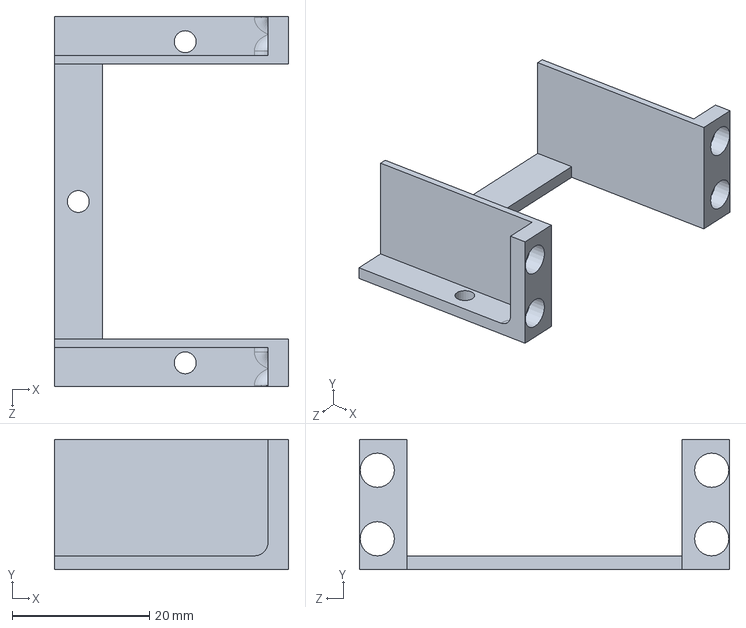
[picture p88: CAD file, 2016-05-19]
Fishing arm/support_servo.SLDPRT
34.2 x 19.0 x 54.0 mm
