OpenRobotics-official/Eurobot-competition/Fishing arm/Support_bras_cylindre.SLDPRT

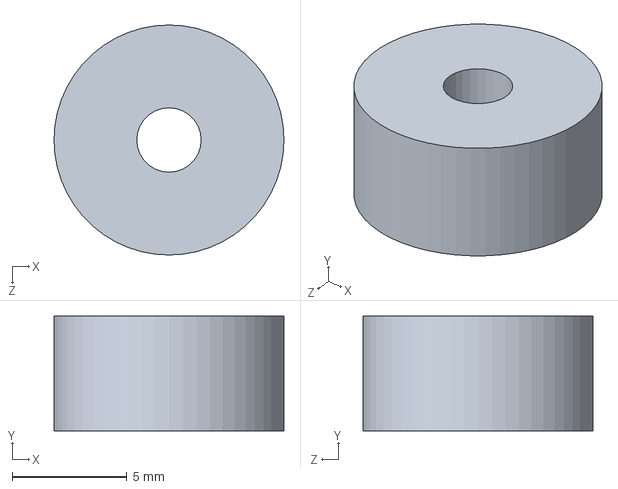
[picture p89: CAD file, 2016-05-19]
Fishing arm/Support_bras_cylindre.SLDPRT
10.0 x 5.00 x 10.0 mm
