OpenRobotics-official/Eurobot-competition/Fishing arm/Plaque_Alu.SLDPRT

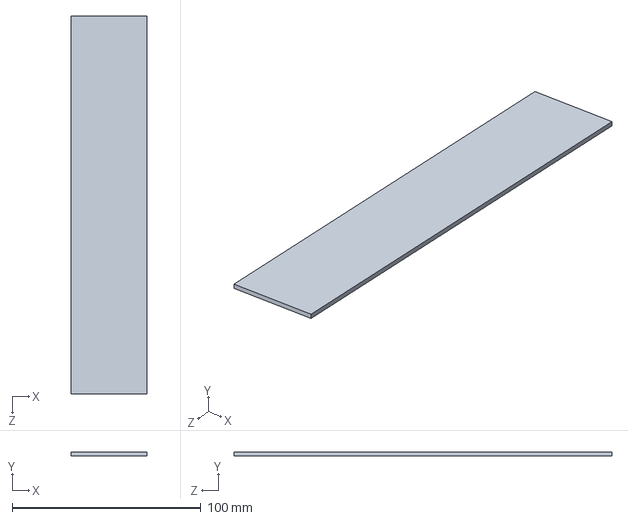
[picture p90: CAD file, 2016-05-19]
Fishing arm/Plaque_Alu.SLDPRT
40.0 x 2.00 x 200.0 mm
