OpenRobotics-official/Eurobot-competition/wheelbase/solidworks/6mm_axle.SLDPRT

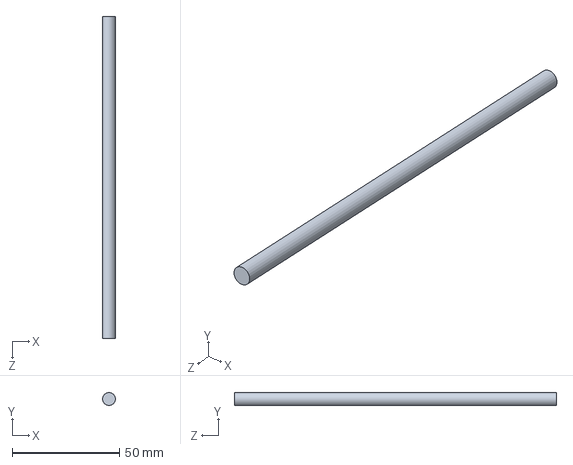
[picture p91: CAD file, 2016-05-19]
wheelbase/solidworks/6mm_axle.SLDPRT
6.00 x 6.00 x 150.0 mm
