OpenRobotics-official/Eurobot-competition/wheelbase/solidworks/Base roulante lucas/outside ball bearing 6.6.19.SLDPRT

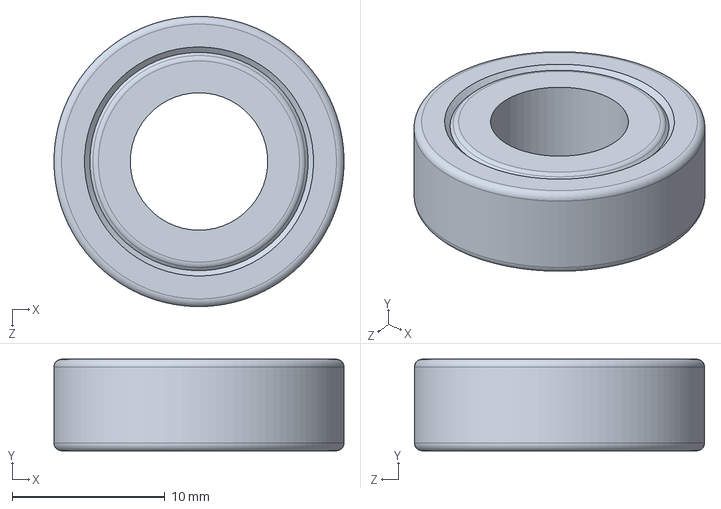
[picture p92: CAD file, 2016-05-19]
wheelbase/solidworks/Base roulante lucas/outside ball bearing 6.6.19.SLDPRT
19.0 x 6.00 x 19.0 mm
