OpenRobotics-official/Eurobot-competition/Fishing arm/Element_Charniere_metal.SLDPRT

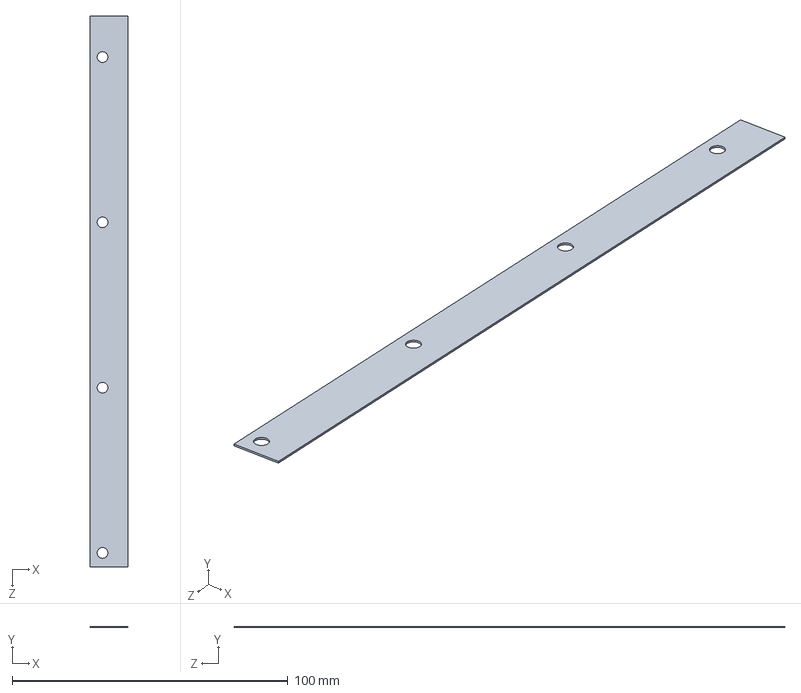
[picture p93: CAD file, 2016-05-19]
Fishing arm/Element_Charniere_metal.SLDPRT
13.7 x 0.5 x 200.0 mm
