OpenRobotics-official/Eurobot-competition/Fishing arm/Aimant.SLDPRT

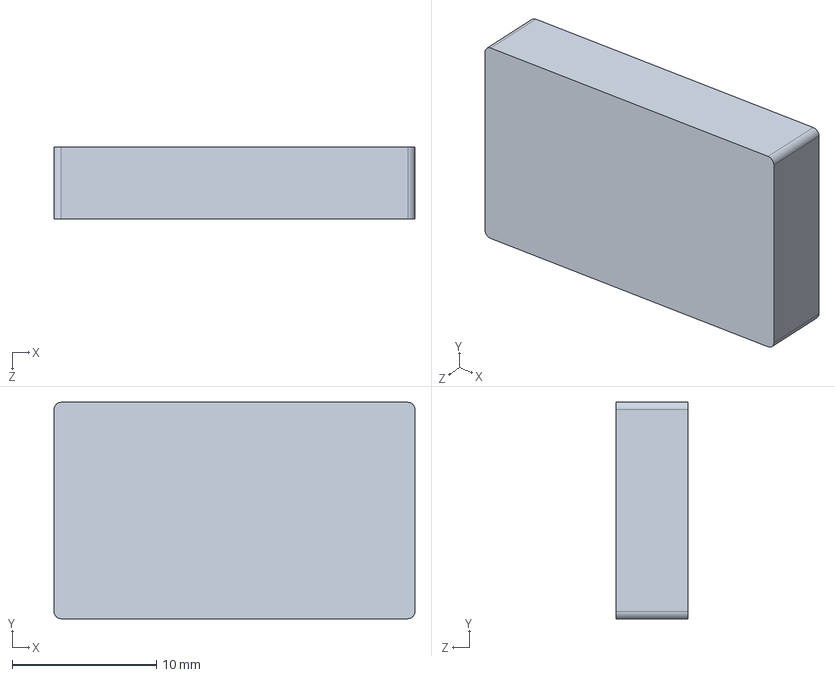
[picture p94: CAD file, 2016-05-19]
Fishing arm/Aimant.SLDPRT
25.0 x 15.0 x 5.00 mm
