OpenRobotics-official/Eurobot-competition/Fishing arm/Charniere_metal.SLDASM

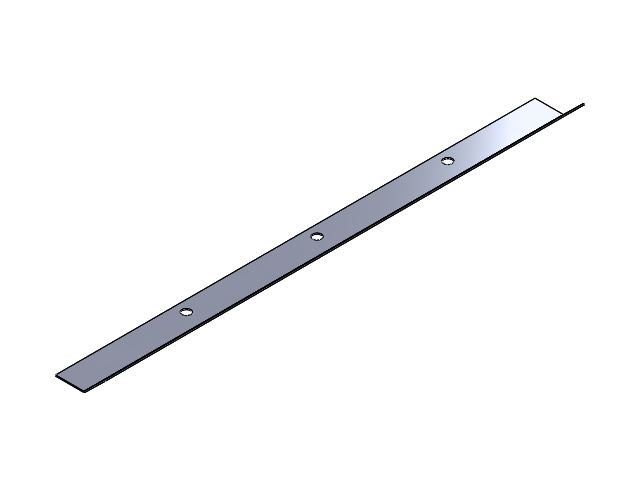
[picture p95: CAD file, 2016-05-19]
Fishing arm/Charniere_metal.SLDASM
Element_Charniere_metal x 2
